JeanetteMueller/OpenPerseverance/images/progress/IMG_1283.jpeg

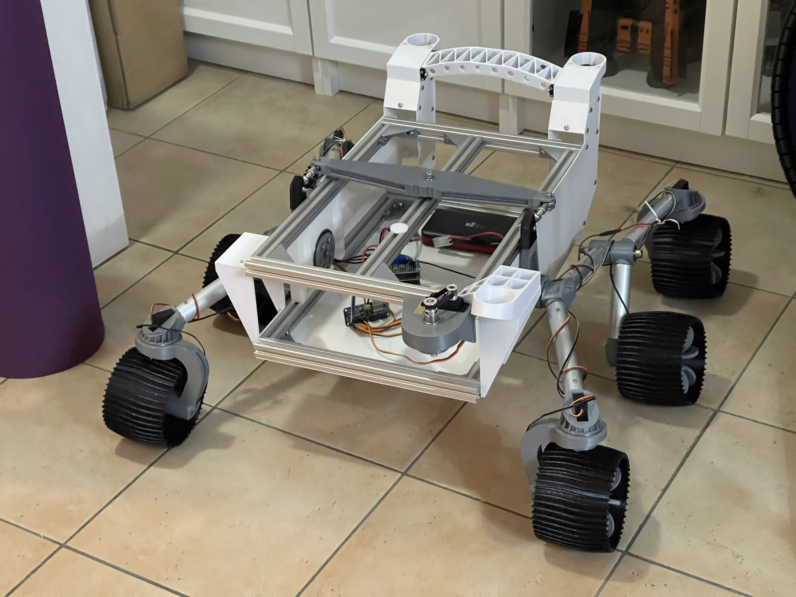
images/progress/IMG_1283.jpeg
