JeanetteMueller/OpenPerseverance/images/progress/IMG_1419.jpeg

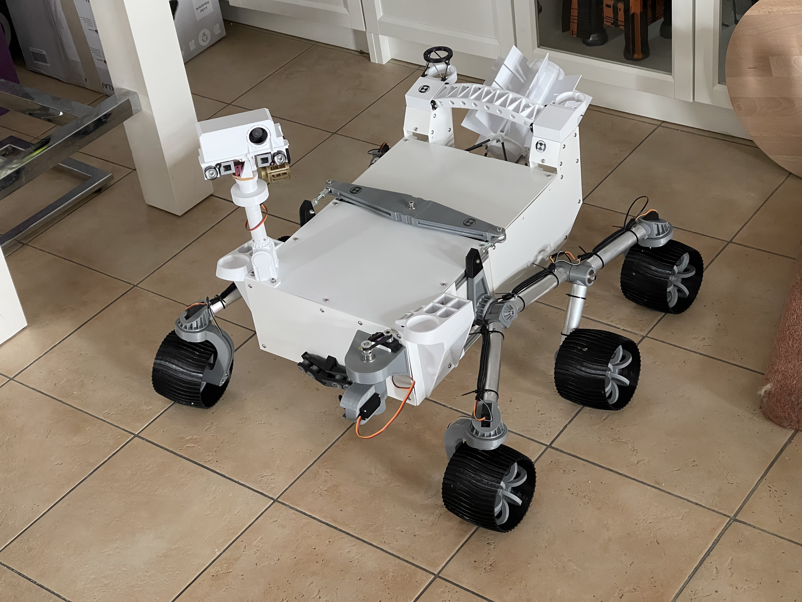
images/progress/IMG_1419.jpeg
