JeanetteMueller/OpenPerseverance/images/progress/IMG_1653.jpeg

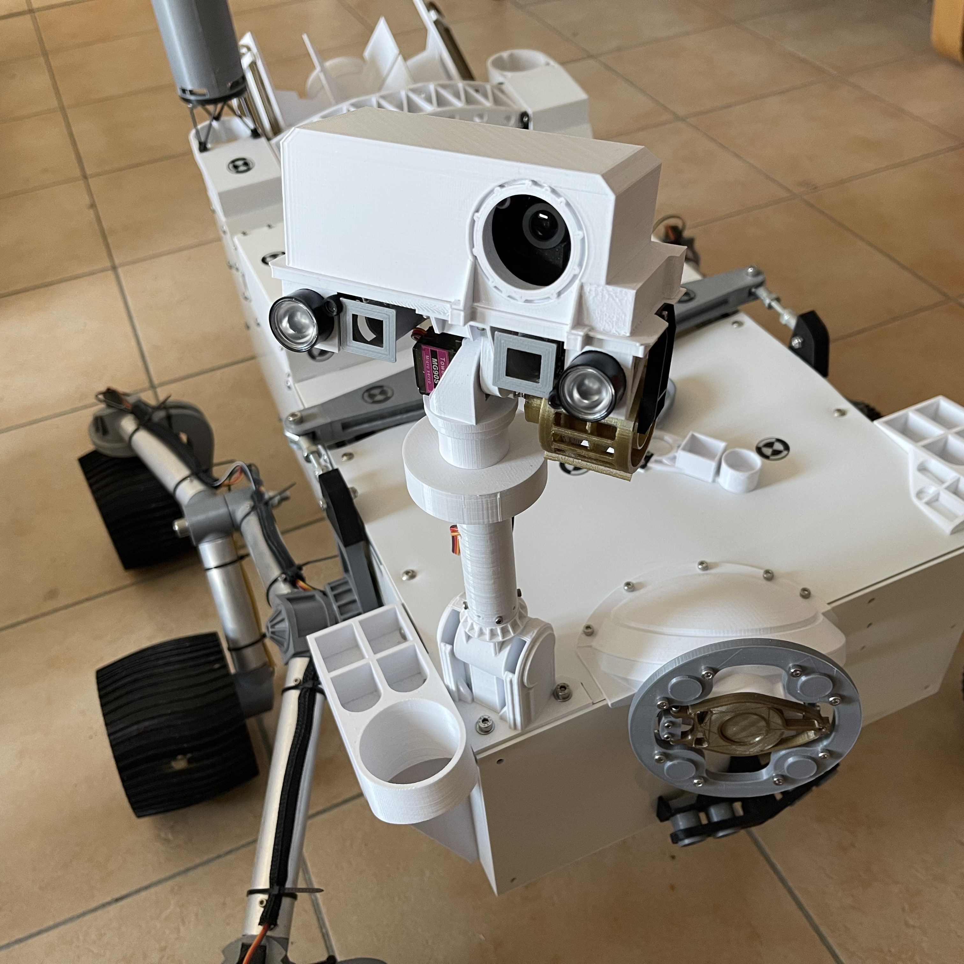
images/progress/IMG_1653.jpeg
