JeanetteMueller/OpenPerseverance/stl/MainBody/SkyCraneConnector/SkyCraneConnector CableCutter.stl

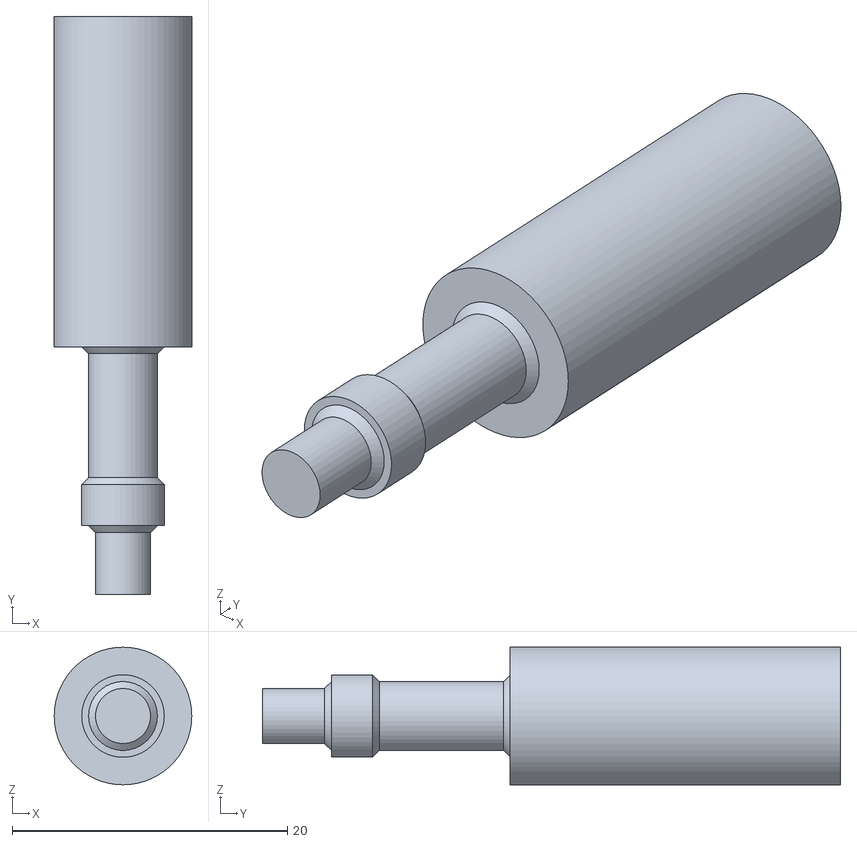
[picture p25: CAD file, 2021-09-22]
stl/MainBody/SkyCraneConnector/SkyCraneConnector CableCutter.stl
10.0 x 42.0 x 10.0
