JeanetteMueller/OpenPerseverance/stl/MainBody/Sundial/SundialBase.stl

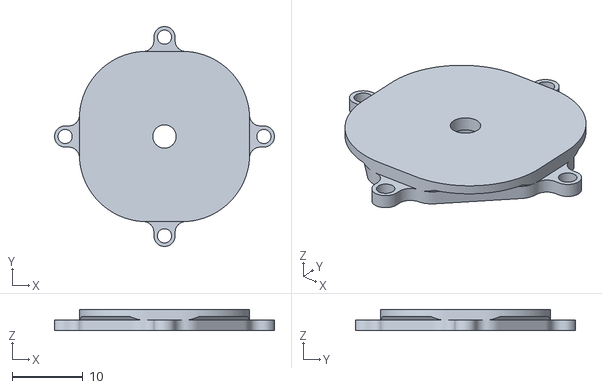
[picture p26: CAD file, 2021-06-23]
stl/MainBody/Sundial/SundialBase.stl
31.0 x 31.0 x 3.00
