JeanetteMueller/OpenPerseverance/stl/MainBody/TopBox/TopBodyBox Back.stl

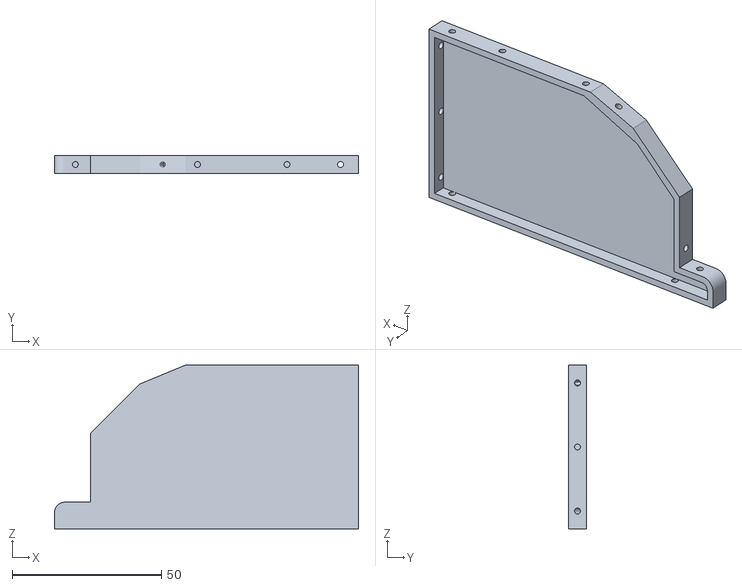
[picture p27: CAD file, 2021-09-22]
stl/MainBody/TopBox/TopBodyBox Back.stl
102.0 x 6.00 x 55.0
