JeanetteMueller/OpenPerseverance/stl/MainBody/UHF/UHF-FootRight.stl

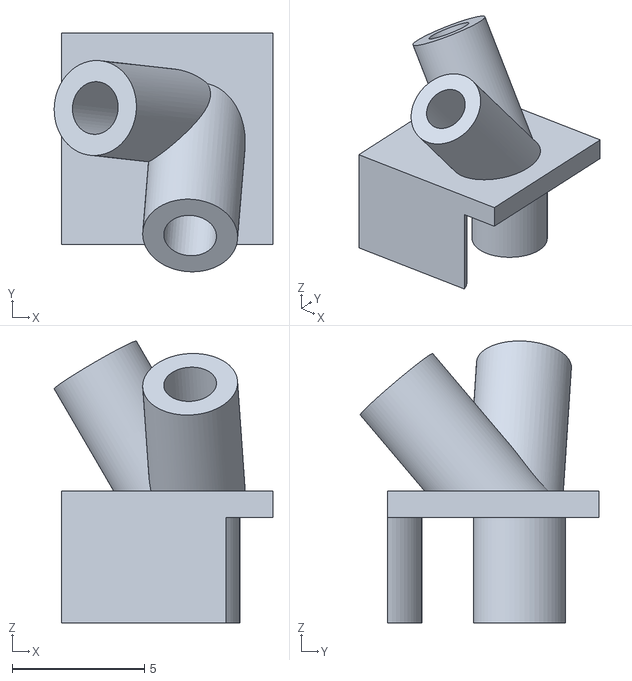
[picture p28: CAD file, 2021-04-29]
stl/MainBody/UHF/UHF-FootRight.stl
8.27 x 9.03 x 10.7
