JeanetteMueller/OpenPerseverance/stl/RockerBogie/CenterRodMount_v2.stl

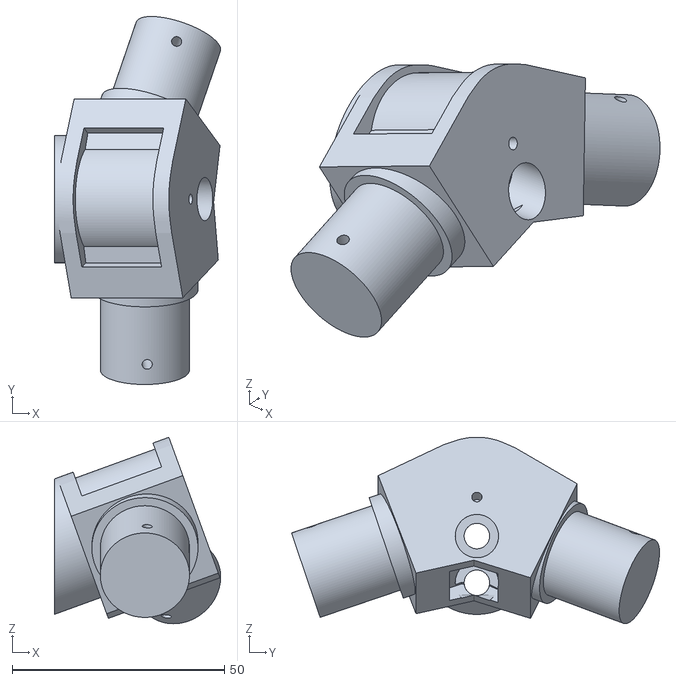
[picture p29: CAD file, 2024-09-03]
stl/RockerBogie/CenterRodMount_v2.stl
39.2 x 86.7 x 43.9
