JeanetteMueller/OpenPerseverance/stl/RockerBogie/UpdatedVersionFor37mmMotor/WheelHolder_Lower.stl

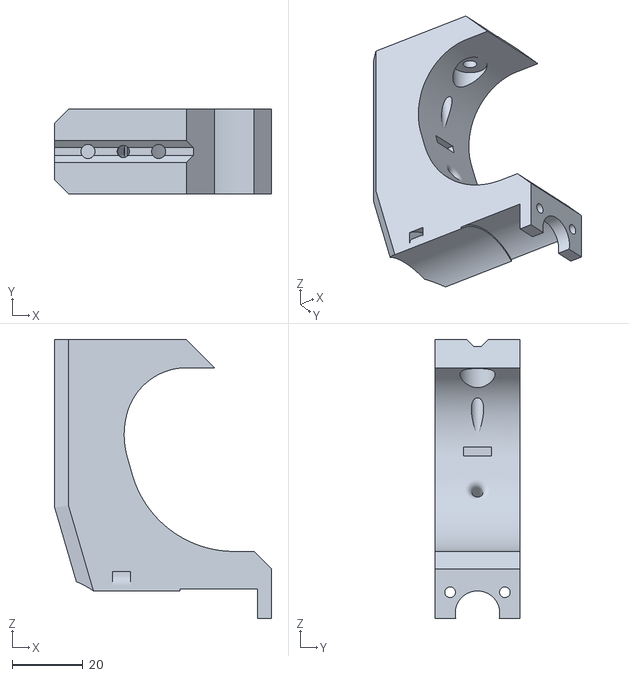
[picture p30: CAD file, 2024-09-03]
stl/RockerBogie/UpdatedVersionFor37mmMotor/WheelHolder_Lower.stl
61.5 x 24.0 x 79.0
