JeanetteMueller/OpenPerseverance/stl/Arm/Hand/HandConnector.stl

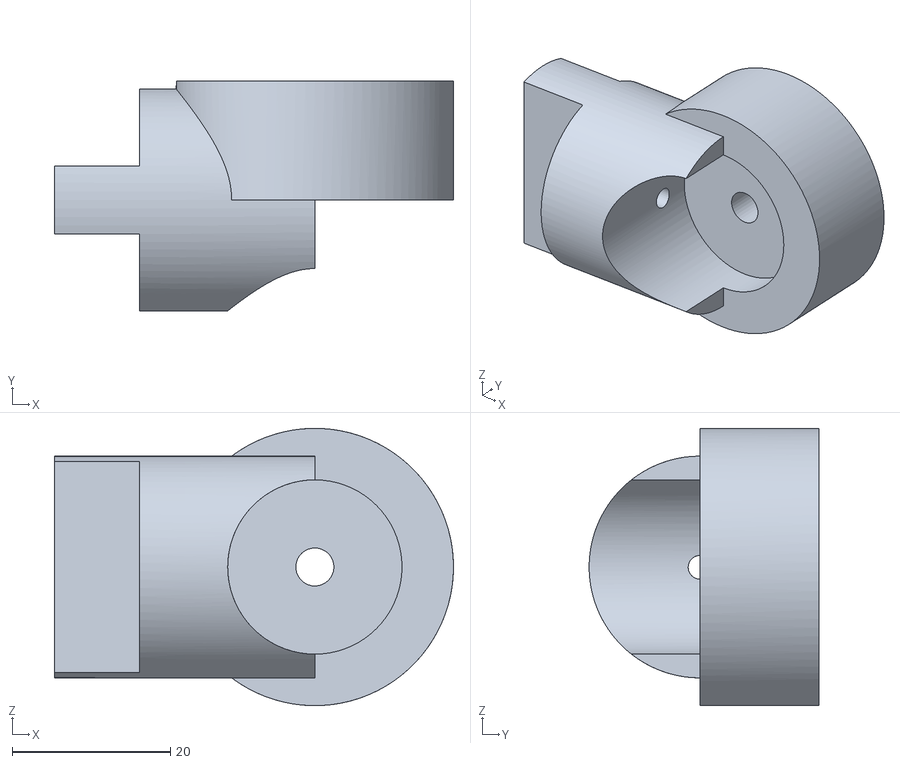
[picture p31: CAD file, 2021-10-04]
stl/Arm/Hand/HandConnector.stl
50.4 x 29.0 x 35.0
