JeanetteMueller/OpenPerseverance/stl/Arm/Instruments/InstrumentsCameraSensor.stl

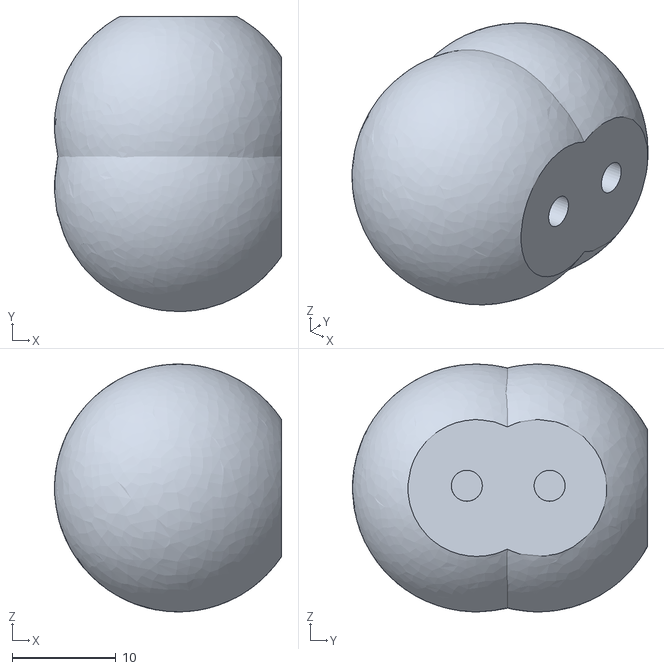
[picture p32: CAD file, 2021-10-04]
stl/Arm/Instruments/InstrumentsCameraSensor.stl
22.0 x 28.5 x 23.9
