JeanetteMueller/OpenPerseverance/stl/Arm/LowerArm/LowerArmAktuator2.stl

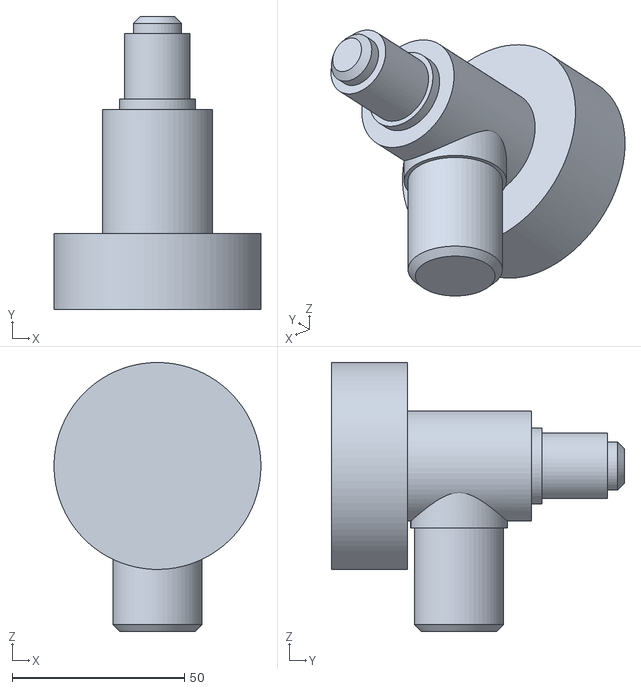
[picture p33: CAD file, 2021-10-04]
stl/Arm/LowerArm/LowerArmAktuator2.stl
60.0 x 85.0 x 78.0
