JeanetteMueller/OpenPerseverance/stl/Arm/NamePlate.stl

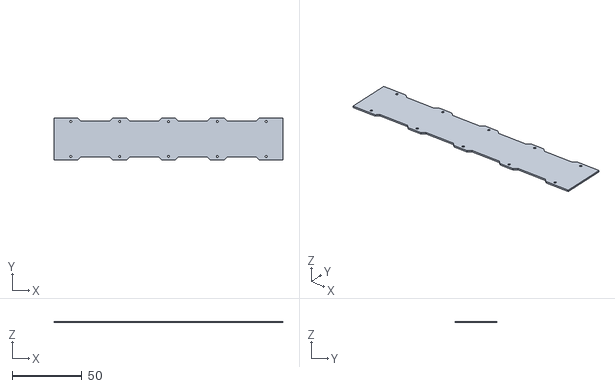
[picture p34: CAD file, 2021-10-04]
stl/Arm/NamePlate.stl
164.0 x 30.0 x 1.00
