JeanetteMueller/OpenPerseverance/stl/Arm/UpperArm/UpperArmRodConnector2.stl

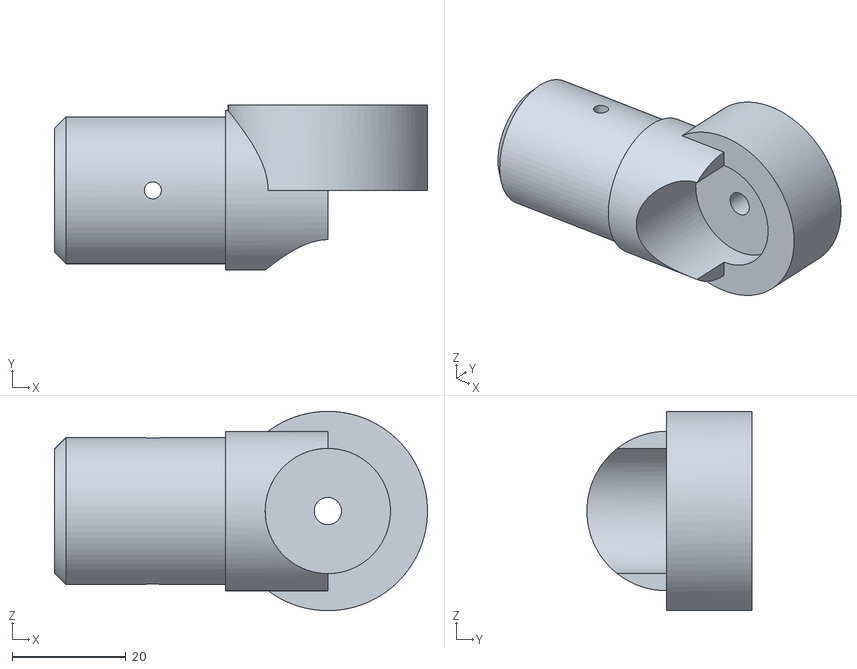
[picture p35: CAD file, 2021-10-04]
stl/Arm/UpperArm/UpperArmRodConnector2.stl
65.5 x 29.0 x 35.0
