JeanetteMueller/OpenPerseverance/stl/HeatExchanger_Left/Heatpipes/HeatExchanger Holder 2.stl

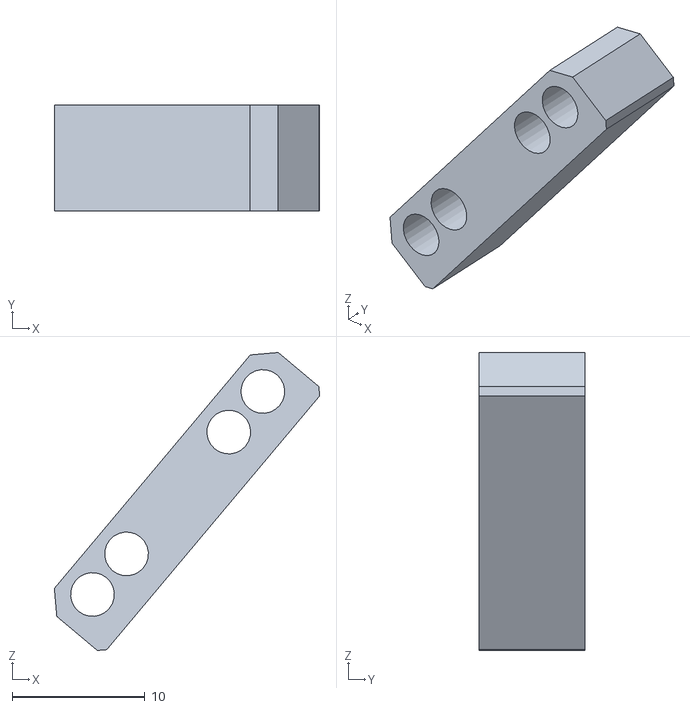
[picture p36: CAD file, 2021-09-22]
stl/HeatExchanger_Left/Heatpipes/HeatExchanger Holder 2.stl
20.0 x 8.00 x 22.5
