JeanetteMueller/OpenPerseverance/stl/HeatExchanger_Left/Holder/HeatExchangerHolder WallMountPoint.stl

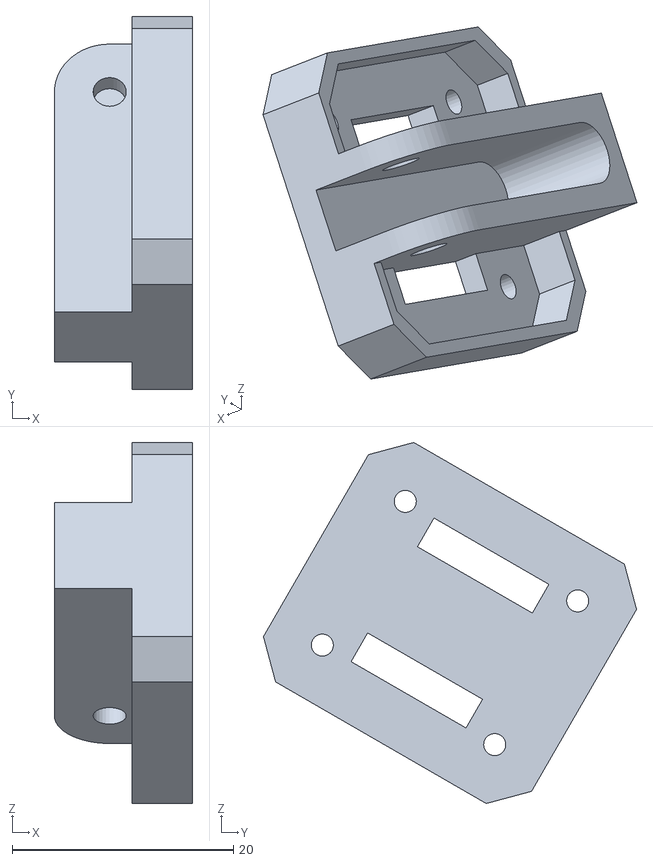
[picture p37: CAD file, 2021-09-22]
stl/HeatExchanger_Left/Holder/HeatExchangerHolder WallMountPoint.stl
12.5 x 33.7 x 32.7
