JeanetteMueller/OpenPerseverance/stl/HeatExchanger_Left/Wall/HeatExchanger Wall_Left_1.stl

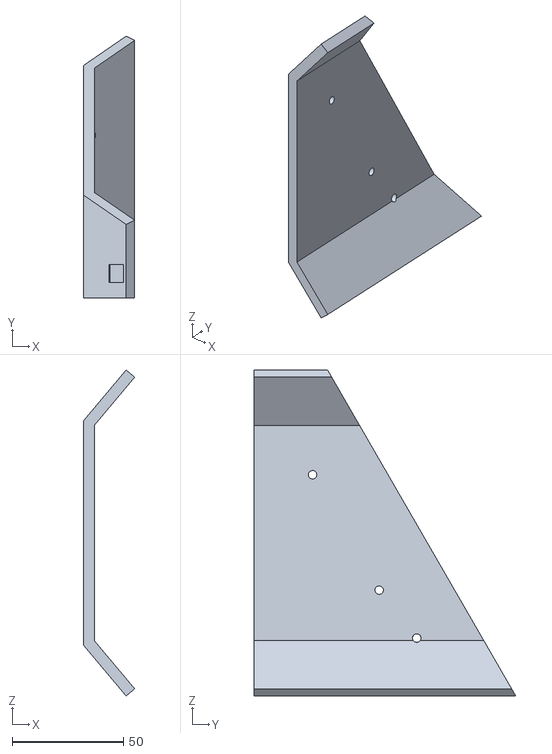
[picture p38: CAD file, 2021-09-22]
stl/HeatExchanger_Left/Wall/HeatExchanger Wall_Left_1.stl
23.2 x 117.8 x 146.8
