JeanetteMueller/OpenPerseverance/stl/MainBody/DifferentialBlocker/DifferentialBlocker Base.stl

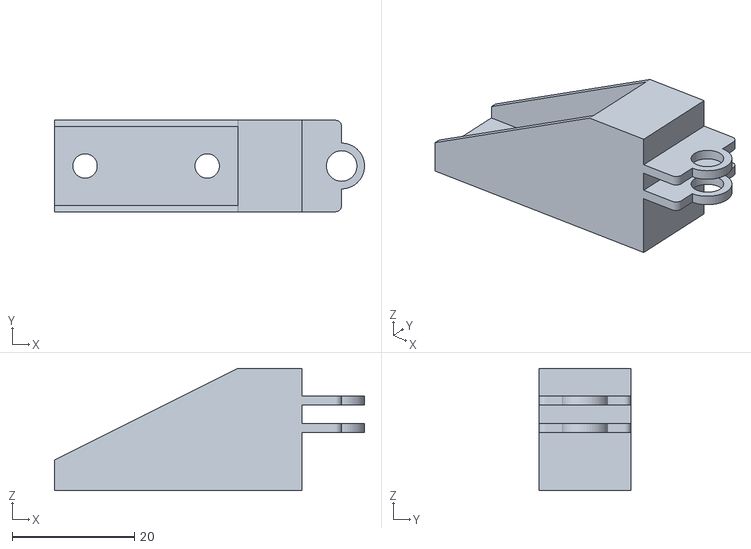
[picture p39: CAD file, 2021-09-22]
stl/MainBody/DifferentialBlocker/DifferentialBlocker Base.stl
50.7 x 15.0 x 20.0
