JeanetteMueller/OpenPerseverance/stl/MainBody/FrontBodyCamera/FrontBodyCamera.stl

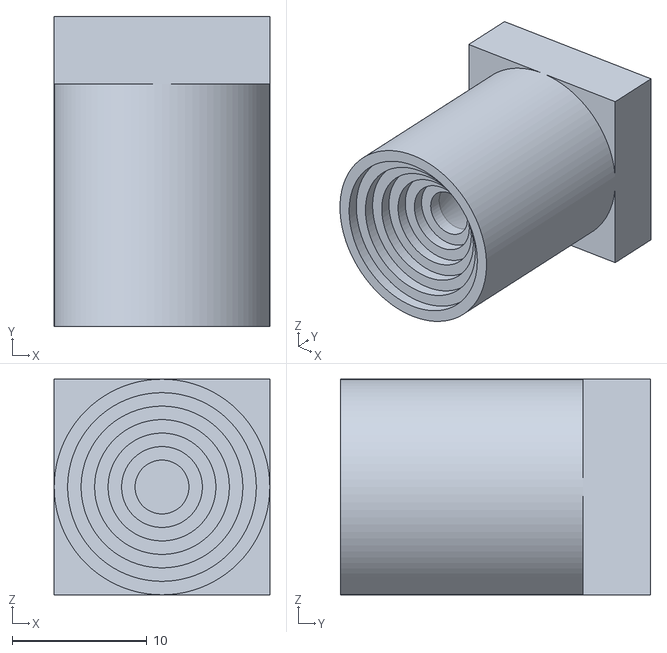
[picture p40: CAD file, 2021-05-07]
stl/MainBody/FrontBodyCamera/FrontBodyCamera.stl
16.0 x 23.0 x 16.0
