JeanetteMueller/OpenPerseverance/stl/MainBody/HighGainAntenna/HighGainAntenna RotationMotor.stl

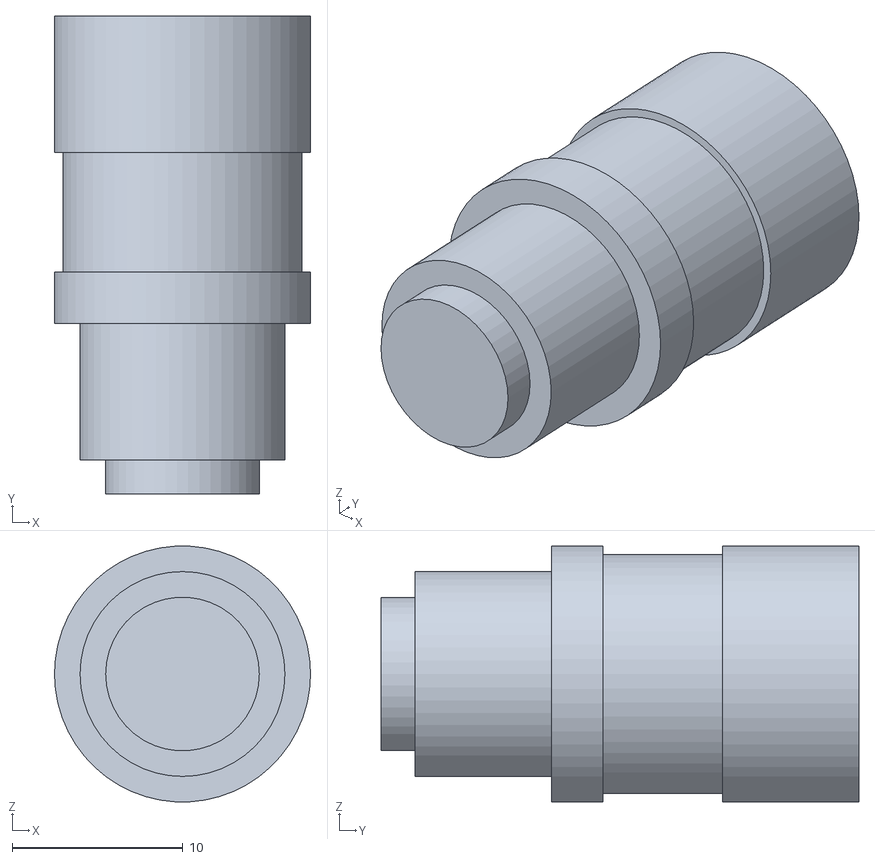
[picture p41: CAD file, 2021-09-22]
stl/MainBody/HighGainAntenna/HighGainAntenna RotationMotor.stl
15.0 x 28.0 x 15.0
