JeanetteMueller/OpenPerseverance/stl/MainBody/LowGainAntenna/LowGainAntenna Mount.stl

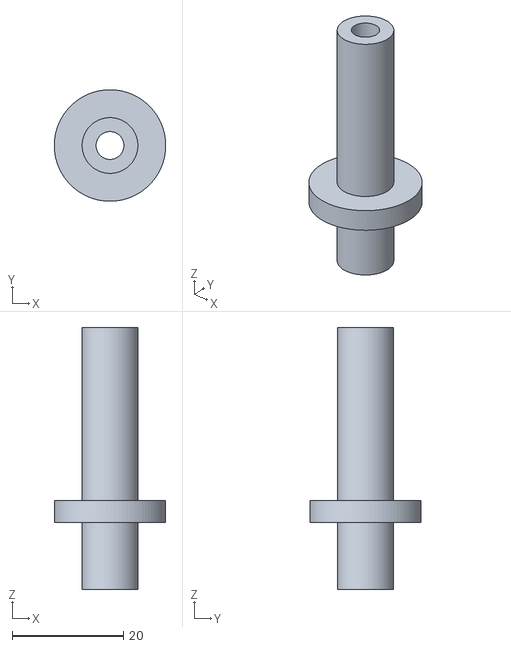
[picture p42: CAD file, 2021-09-22]
stl/MainBody/LowGainAntenna/LowGainAntenna Mount.stl
20.0 x 20.0 x 47.0
