JeanetteMueller/OpenPerseverance/stl/MainBody/SampleCollector/HatchHolderOuter.stl

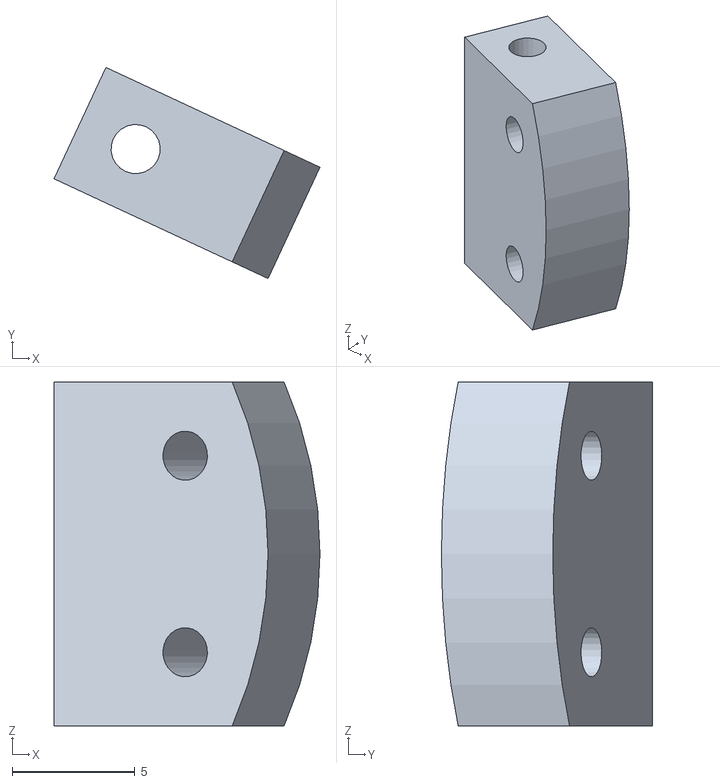
[picture p43: CAD file, 2021-06-20]
stl/MainBody/SampleCollector/HatchHolderOuter.stl
10.8 x 8.59 x 14.0
