JeanetteMueller/OpenPerseverance/stl/MainBody/ShellToProfileConnector.stl

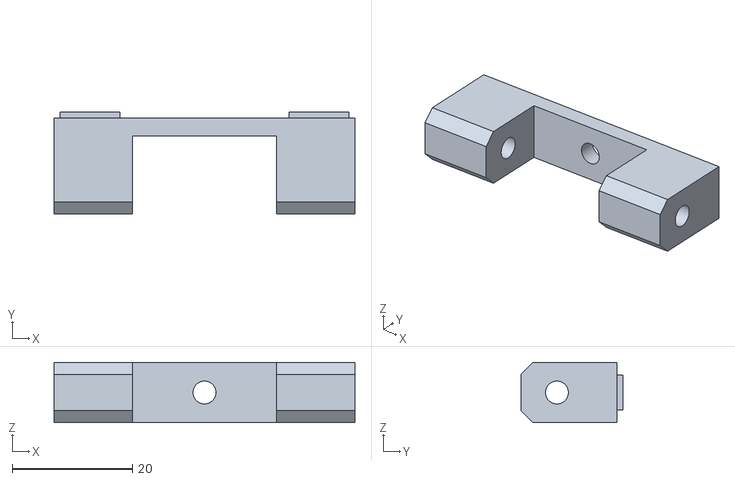
[picture p44: CAD file, 2021-04-29]
stl/MainBody/ShellToProfileConnector.stl
50.0 x 17.0 x 10.0
