JeanetteMueller/OpenPerseverance/stl/MainBody/SkyCraneConnector/SkyCraneConnector Base.stl

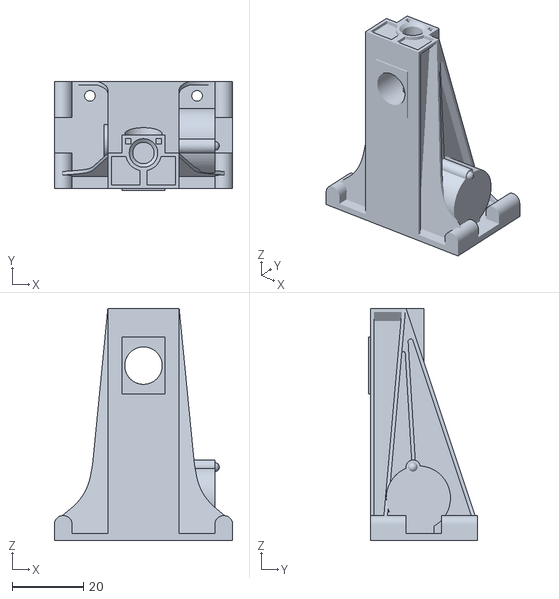
[picture p45: CAD file, 2021-09-22]
stl/MainBody/SkyCraneConnector/SkyCraneConnector Base.stl
50.0 x 30.5 x 65.0
