JeanetteMueller/OpenPerseverance/stl/MainBody/Sundial/SundialPin.stl

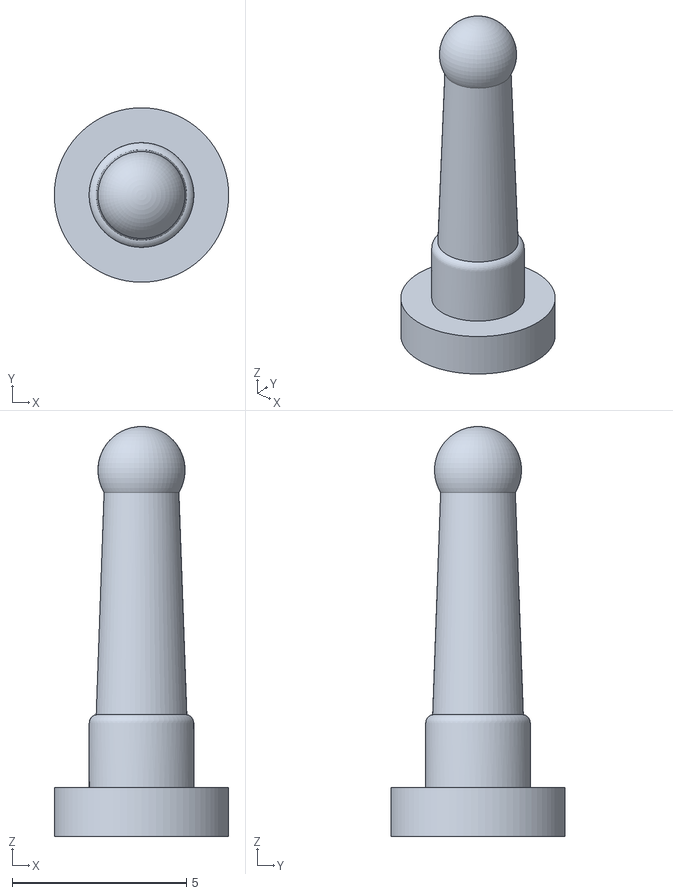
[picture p46: CAD file, 2021-06-23]
stl/MainBody/Sundial/SundialPin.stl
5.00 x 5.00 x 11.8
