JeanetteMueller/OpenPerseverance/stl/RockerBogie/DifferentialMount_v2.stl

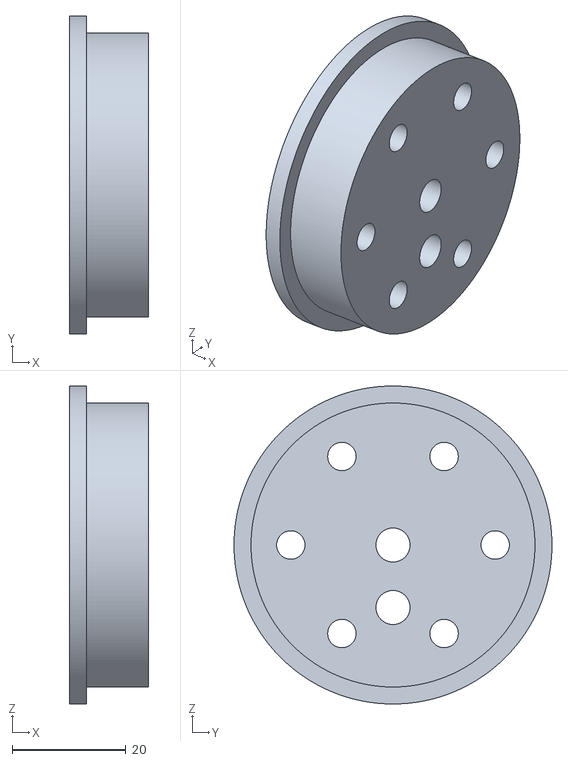
[picture p47: CAD file, 2024-09-03]
stl/RockerBogie/DifferentialMount_v2.stl
14.0 x 56.0 x 56.0
