JeanetteMueller/OpenPerseverance/stl/RockerBogie/UpdatedVersionFor37mmMotor/WheelHolderCenter.stl

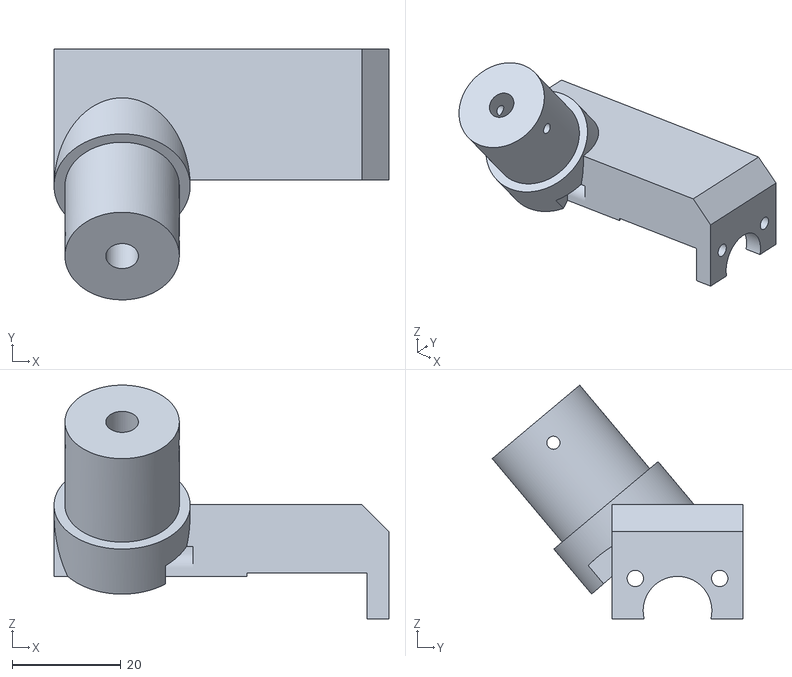
[picture p48: CAD file, 2024-09-03]
stl/RockerBogie/UpdatedVersionFor37mmMotor/WheelHolderCenter.stl
61.5 x 46.0 x 42.9
