JeanetteMueller/OpenPerseverance/stl/Arm/ArmStandReferencesMount.stl

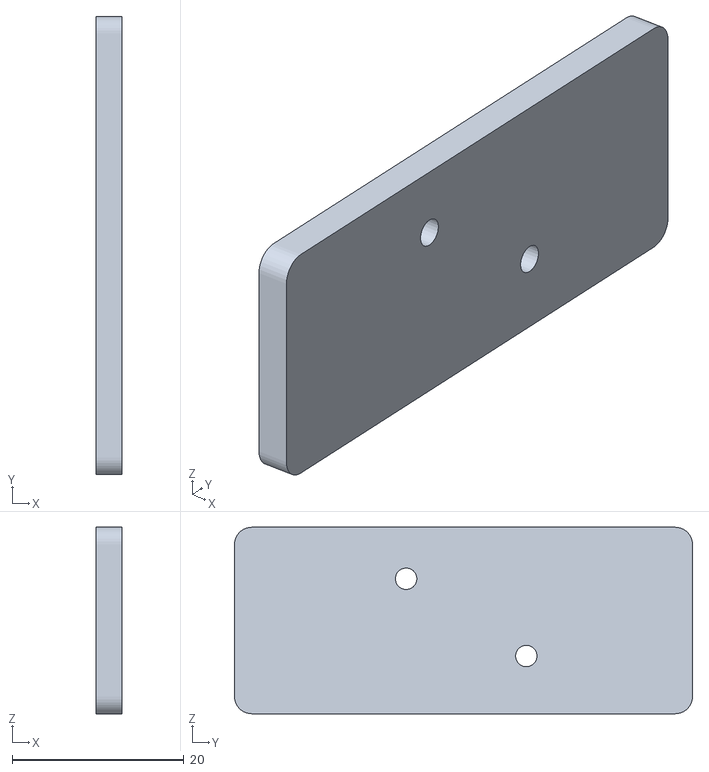
[picture p49: CAD file, 2021-10-04]
stl/Arm/ArmStandReferencesMount.stl
3.00 x 53.3 x 21.7
