JeanetteMueller/OpenPerseverance/stl/Arm/Instruments/InstrumentsSherlocWatsonBody.stl

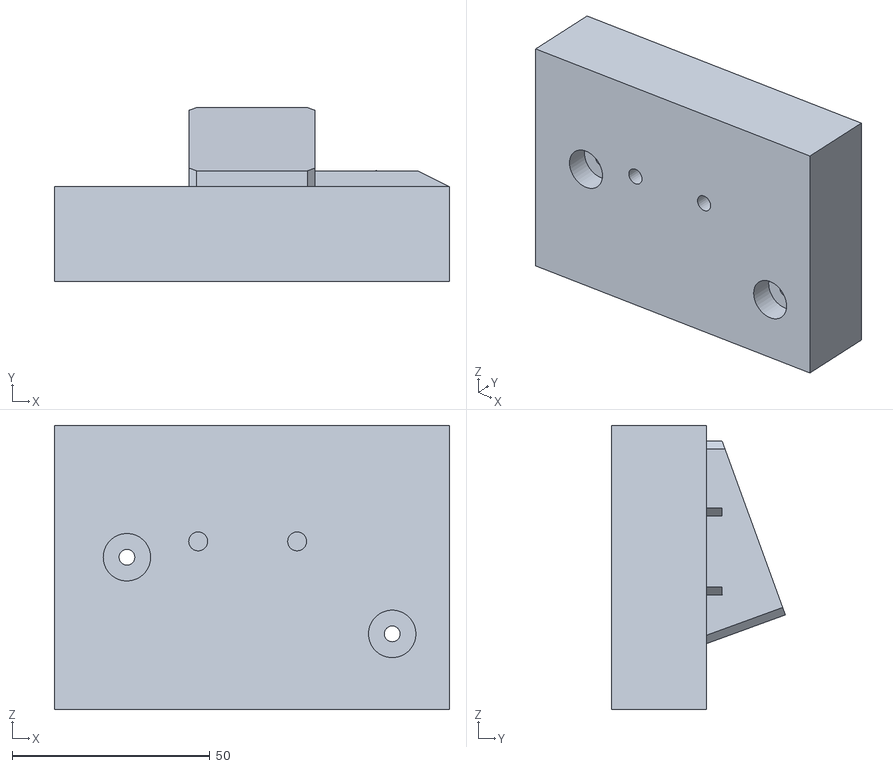
[picture p50: CAD file, 2021-10-04]
stl/Arm/Instruments/InstrumentsSherlocWatsonBody.stl
99.8 x 43.9 x 71.9
