JeanetteMueller/OpenPerseverance/stl/Arm/UpperArm/UpperArmAktuator2.stl

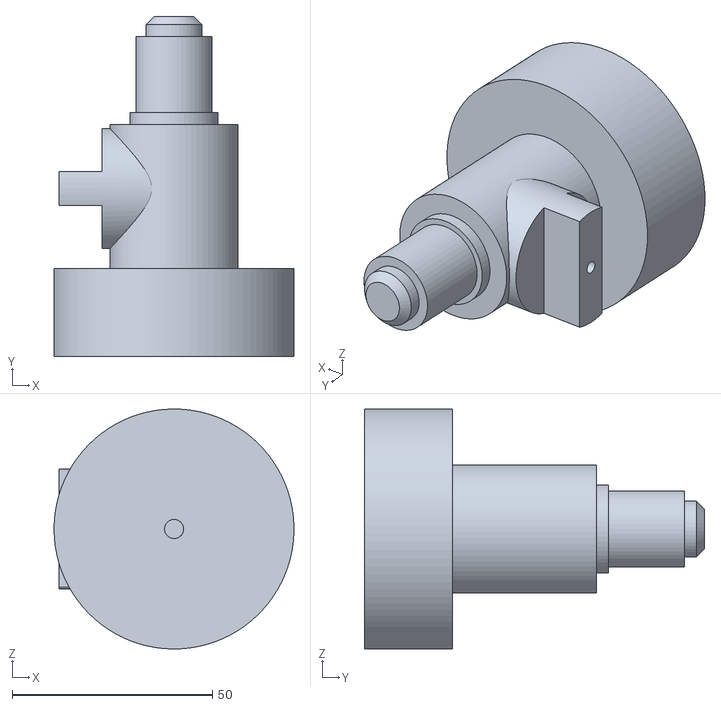
[picture p51: CAD file, 2021-10-04]
stl/Arm/UpperArm/UpperArmAktuator2.stl
60.0 x 85.0 x 60.0
