JeanetteMueller/OpenPerseverance/stl/HeatExchanger_Left/Heatpipes/HeatExchanger Holder 8.stl

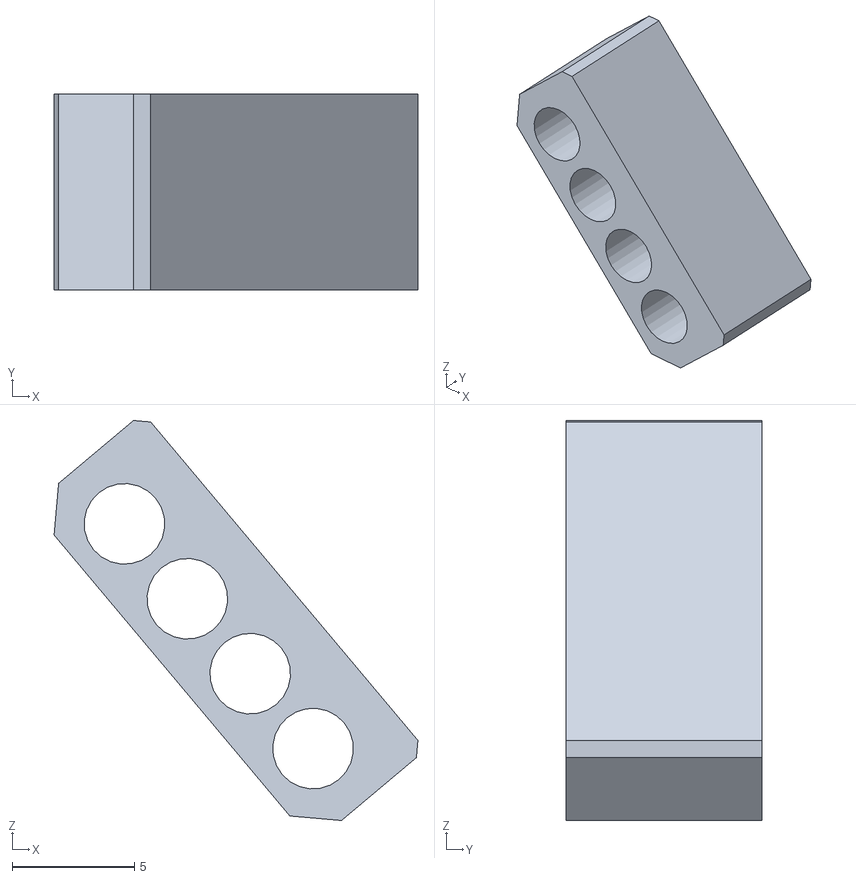
[picture p52: CAD file, 2021-09-22]
stl/HeatExchanger_Left/Heatpipes/HeatExchanger Holder 8.stl
14.9 x 8.00 x 16.4
