JeanetteMueller/OpenPerseverance/stl/HeatExchanger_Left/Holder/HeatExchangerHolder Connector.stl

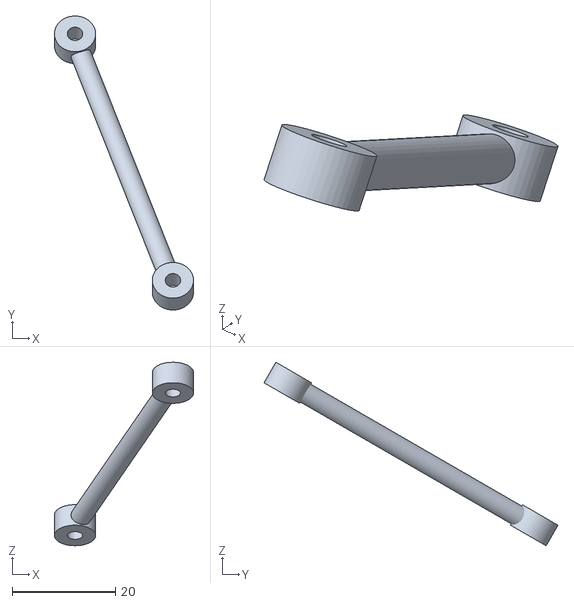
[picture p53: CAD file, 2021-09-22]
stl/HeatExchanger_Left/Holder/HeatExchangerHolder Connector.stl
27.0 x 57.1 x 35.6
