JeanetteMueller/OpenPerseverance/stl/MainBody/HighGainAntenna/HighGainAntenna RotationBase.stl

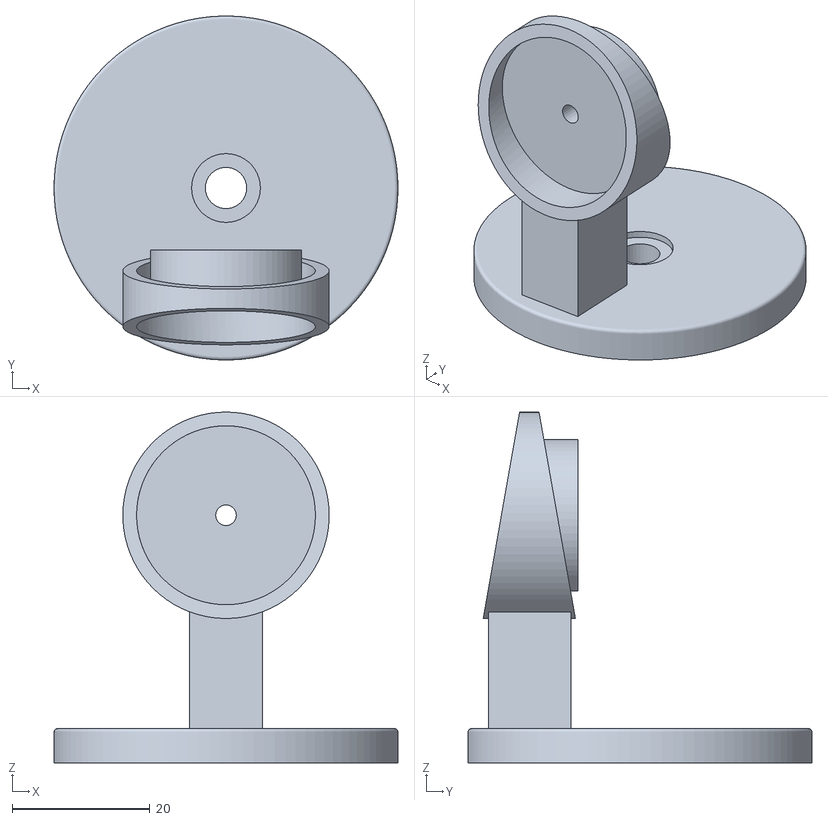
[picture p54: CAD file, 2021-09-22]
stl/MainBody/HighGainAntenna/HighGainAntenna RotationBase.stl
50.0 x 50.0 x 51.0
