JeanetteMueller/OpenPerseverance/stl/MainBody/LowGainAntenna/LowGainAntenna Foot.stl

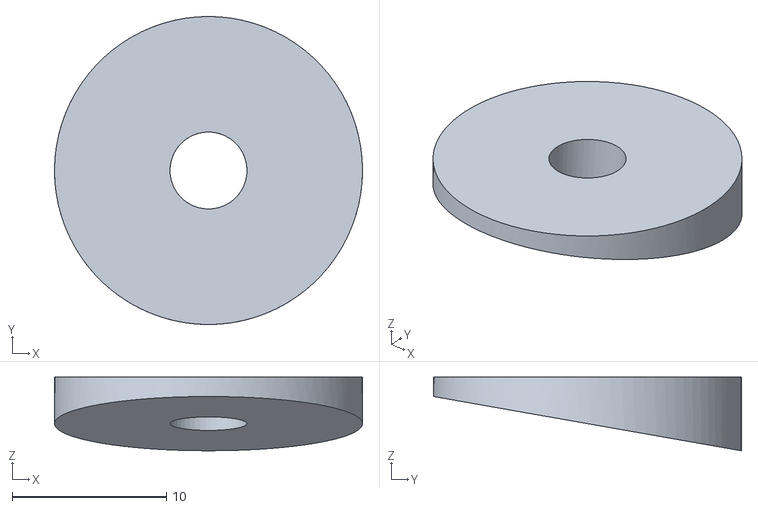
[picture p55: CAD file, 2021-09-22]
stl/MainBody/LowGainAntenna/LowGainAntenna Foot.stl
20.0 x 20.0 x 4.78
