JeanetteMueller/OpenPerseverance/stl/MainBody/SampleCollector/HatchHolderInner.stl

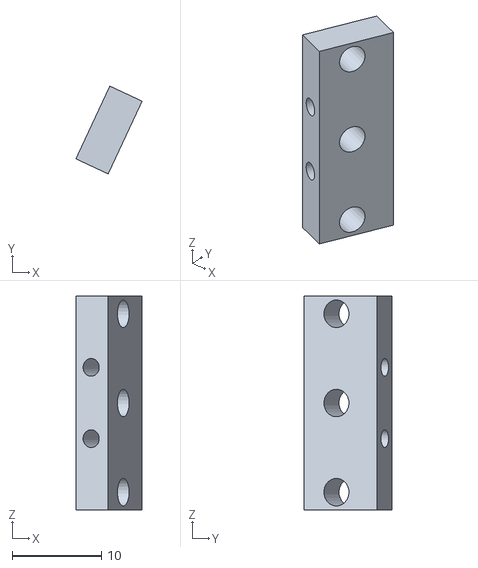
[picture p56: CAD file, 2021-06-20]
stl/MainBody/SampleCollector/HatchHolderInner.stl
7.43 x 9.85 x 24.0
