JeanetteMueller/OpenPerseverance/stl/MainBody/ShellConnector.stl

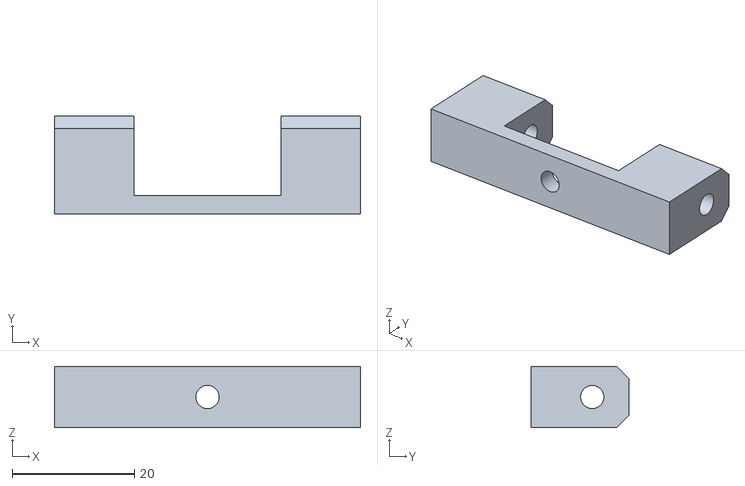
[picture p57: CAD file, 2021-04-29]
stl/MainBody/ShellConnector.stl
50.0 x 16.0 x 10.0
