JeanetteMueller/OpenPerseverance/stl/MainBody/UHF/UHF-MountingRing.stl

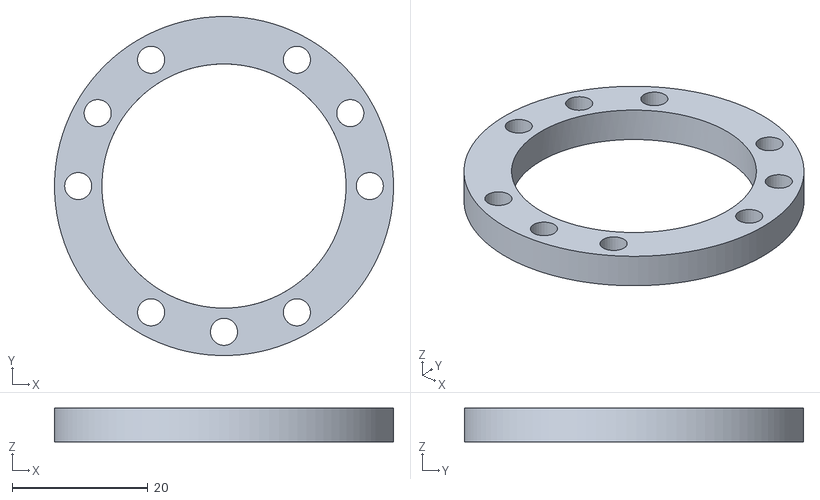
[picture p58: CAD file, 2021-04-29]
stl/MainBody/UHF/UHF-MountingRing.stl
50.0 x 50.0 x 5.00
