JeanetteMueller/OpenPerseverance/stl/RockerBogie/BalanceArmBlockerHead.stl

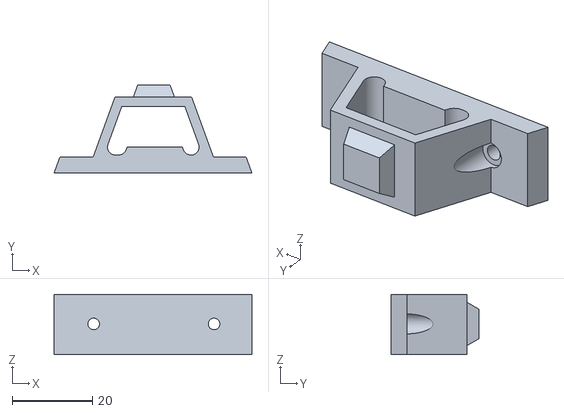
[picture p59: CAD file, 2022-03-11]
stl/RockerBogie/BalanceArmBlockerHead.stl
49.3 x 22.0 x 15.0
