JeanetteMueller/OpenPerseverance/stl/RockerBogie/UpdatedVersionFor37mmMotor/WheelHolder_Top.stl

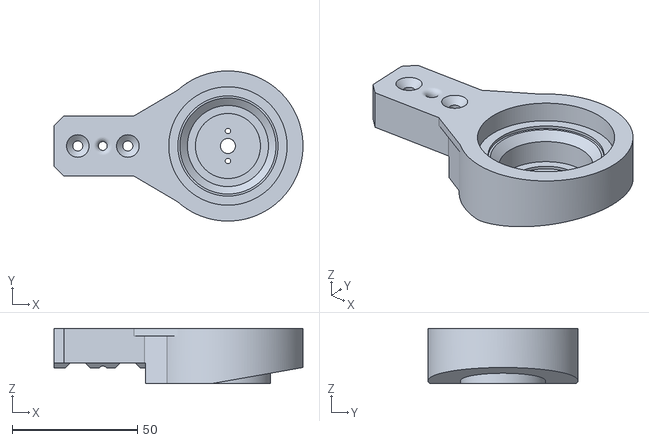
[picture p60: CAD file, 2024-09-03]
stl/RockerBogie/UpdatedVersionFor37mmMotor/WheelHolder_Top.stl
99.5 x 60.0 x 22.0
