JeanetteMueller/OpenPerseverance/stl/Arm/ArmHolder.stl

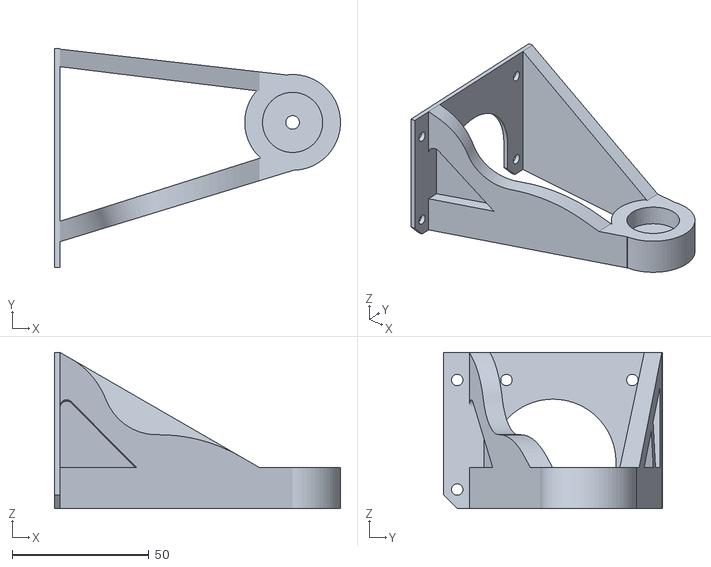
[picture p61: CAD file, 2021-10-04]
stl/Arm/ArmHolder.stl
104.5 x 80.0 x 57.1
