JeanetteMueller/OpenPerseverance/stl/Arm/Instruments/InstrumentsBaseplateConnector.stl

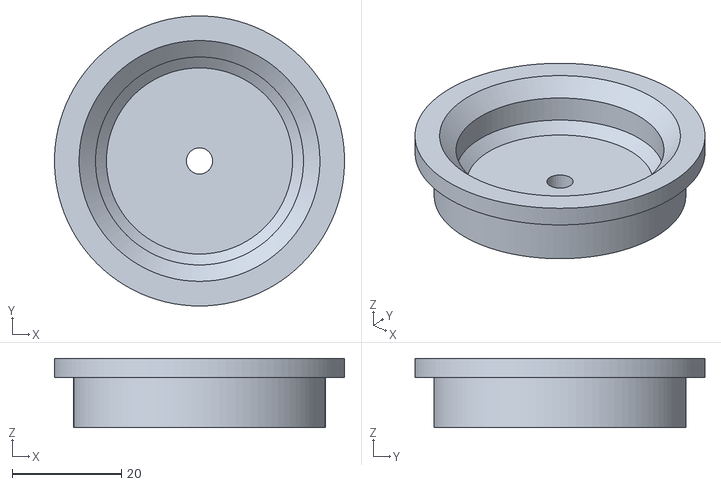
[picture p62: CAD file, 2021-10-04]
stl/Arm/Instruments/InstrumentsBaseplateConnector.stl
53.0 x 53.0 x 12.7
