JeanetteMueller/OpenPerseverance/stl/HeatExchanger_Left/Heatpipes/HeatExchanger Holder 3.stl

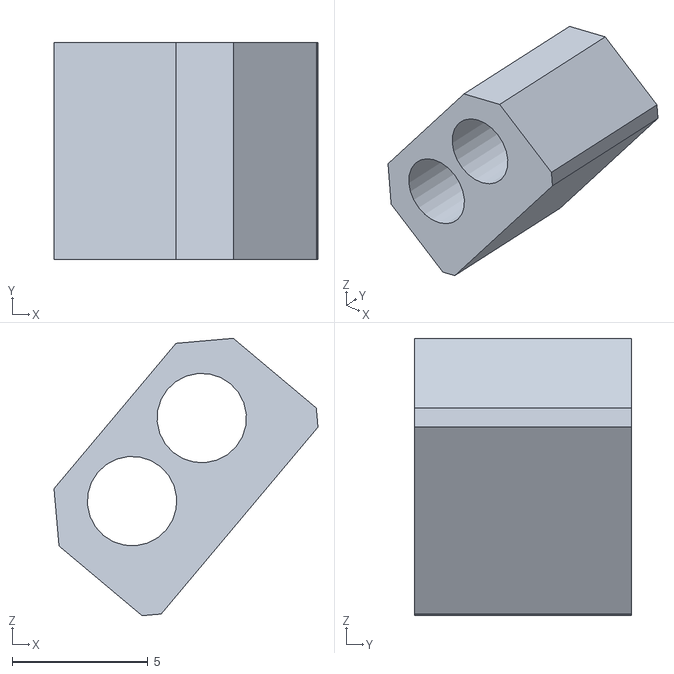
[picture p63: CAD file, 2021-09-22]
stl/HeatExchanger_Left/Heatpipes/HeatExchanger Holder 3.stl
9.74 x 8.00 x 10.2
