JeanetteMueller/OpenPerseverance/stl/MainBody/DifferentialBodyMount_v1.stl

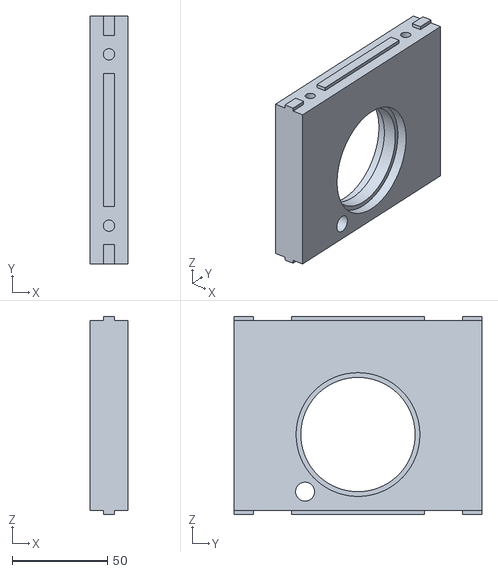
[picture p64: CAD file, 2021-04-12]
stl/MainBody/DifferentialBodyMount_v1.stl
20.0 x 130.0 x 104.0
