JeanetteMueller/OpenPerseverance/stl/MainBody/HighGainAntenna/HighGainAntenna RecieverPlate.stl

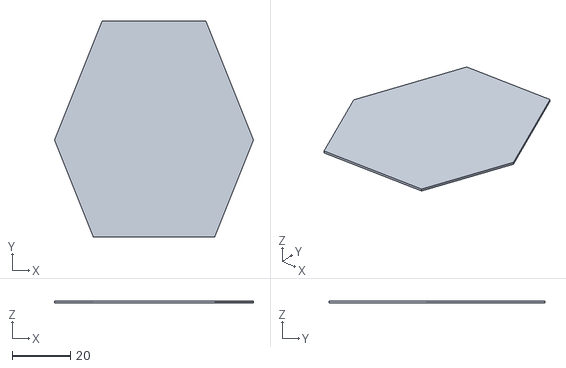
[picture p65: CAD file, 2021-09-22]
stl/MainBody/HighGainAntenna/HighGainAntenna RecieverPlate.stl
68.2 x 74.0 x 0.75
