JeanetteMueller/OpenPerseverance/stl/MainBody/SampleCollector/Hatch.stl

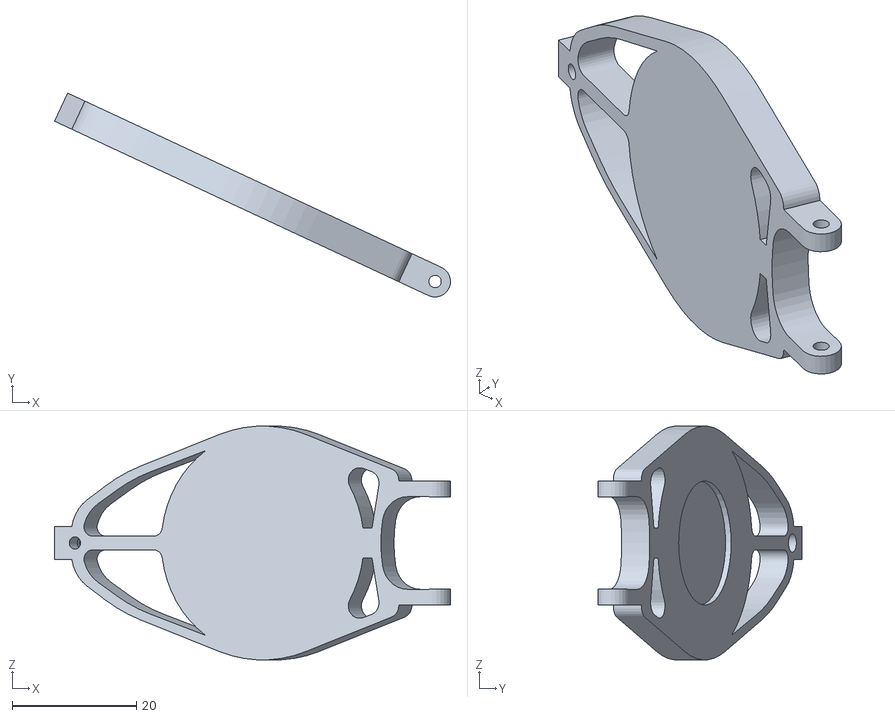
[picture p66: CAD file, 2021-06-20]
stl/MainBody/SampleCollector/Hatch.stl
63.8 x 32.9 x 37.6
