JeanetteMueller/OpenPerseverance/stl/MainBody/UHF/UHF-FootCenter.stl

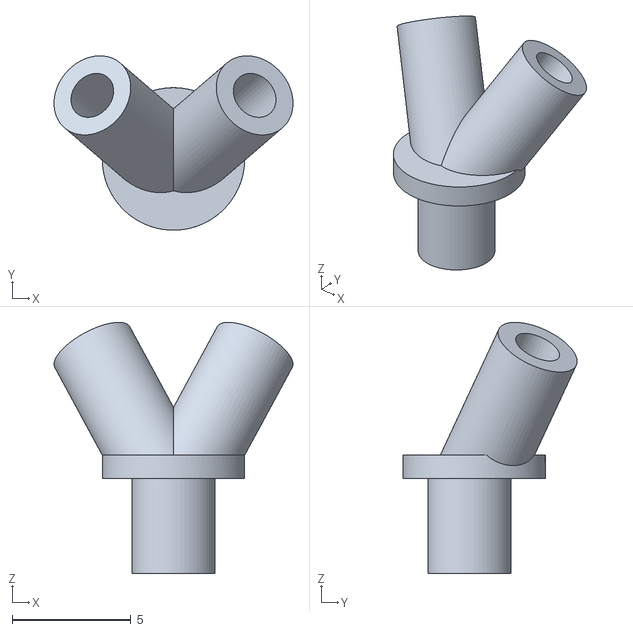
[picture p67: CAD file, 2021-04-29]
stl/MainBody/UHF/UHF-FootCenter.stl
10.1 x 7.34 x 10.6
