JeanetteMueller/OpenPerseverance/stl/RockerBogie/BalanceArmCenter.stl

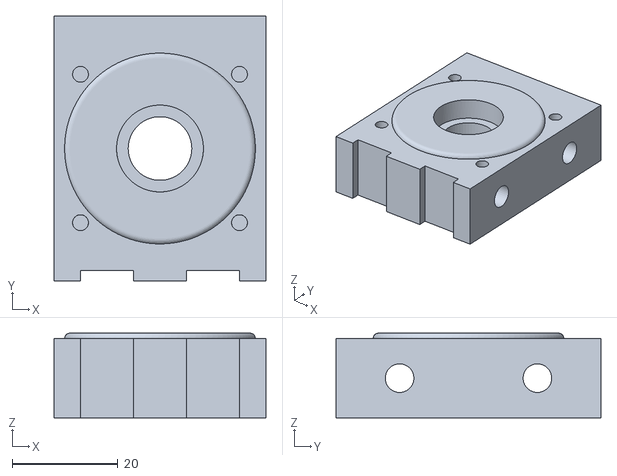
[picture p68: CAD file, 2022-03-11]
stl/RockerBogie/BalanceArmCenter.stl
40.0 x 50.0 x 16.0
