JeanetteMueller/OpenPerseverance/stl/RockerBogie/UpdatedVersionFor37mmMotor/WheelHolderServoConnector.stl

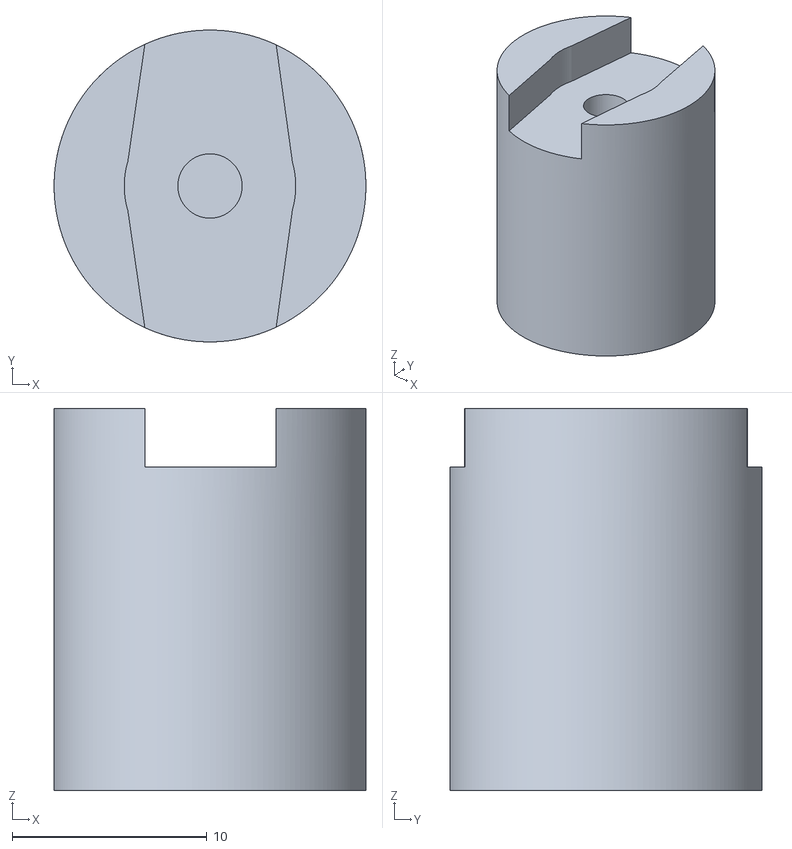
[picture p69: CAD file, 2024-09-03]
stl/RockerBogie/UpdatedVersionFor37mmMotor/WheelHolderServoConnector.stl
16.0 x 16.0 x 19.6
