JeanetteMueller/OpenPerseverance/stl/Arm/ArmStand.stl

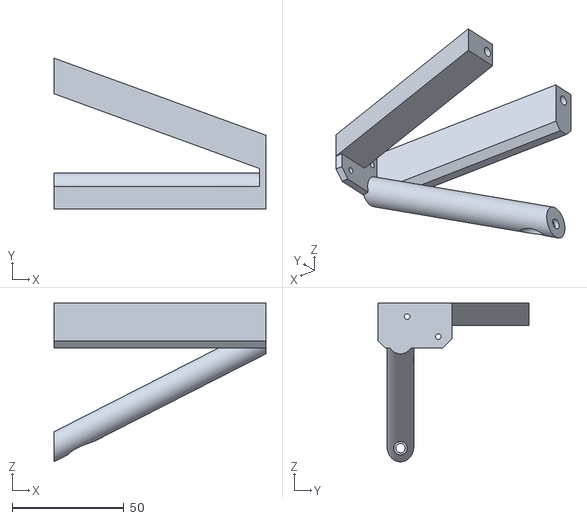
[picture p70: CAD file, 2021-10-04]
stl/Arm/ArmStand.stl
95.0 x 67.6 x 71.1
