JeanetteMueller/OpenPerseverance/stl/Arm/Instruments/InstrumentsPixl.stl

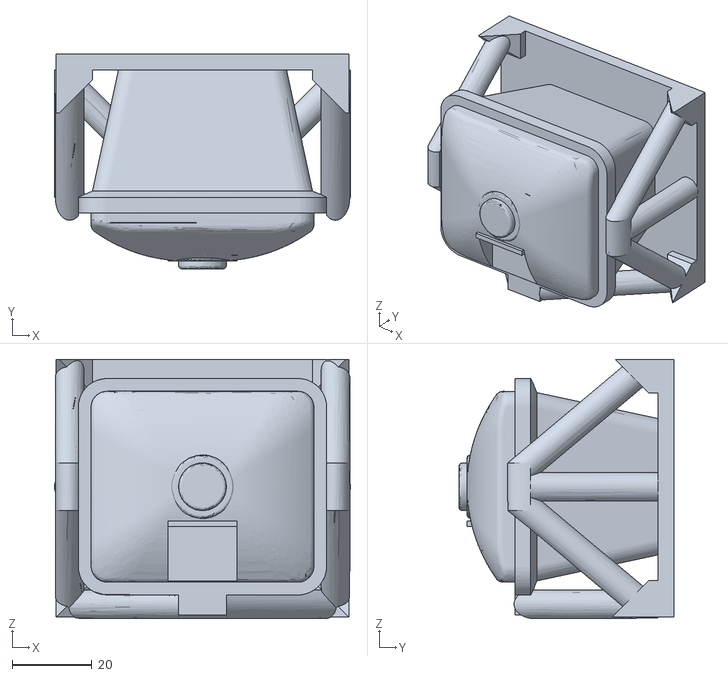
[picture p71: CAD file, 2021-10-04]
stl/Arm/Instruments/InstrumentsPixl.stl
74.3 x 53.9 x 65.0
