JeanetteMueller/OpenPerseverance/stl/MainBody/HighGainAntenna/HighGainAntenna TransportLock.stl

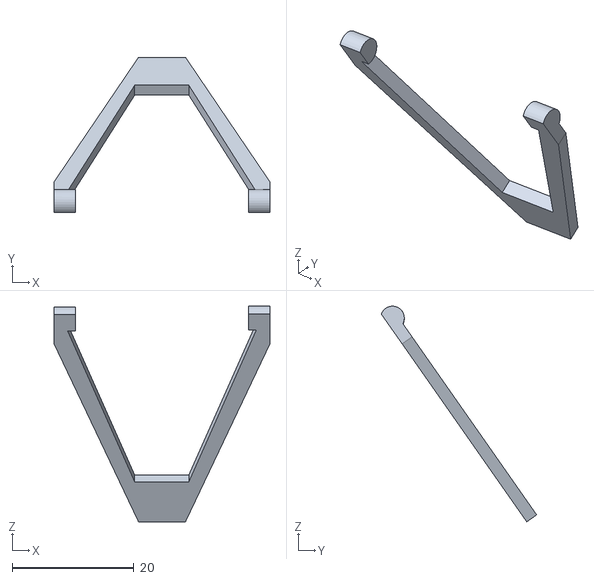
[picture p72: CAD file, 2021-09-22]
stl/MainBody/HighGainAntenna/HighGainAntenna TransportLock.stl
35.5 x 25.5 x 35.4
