JeanetteMueller/OpenPerseverance/stl/MainBody/SampleCollector/CollectorTop.stl

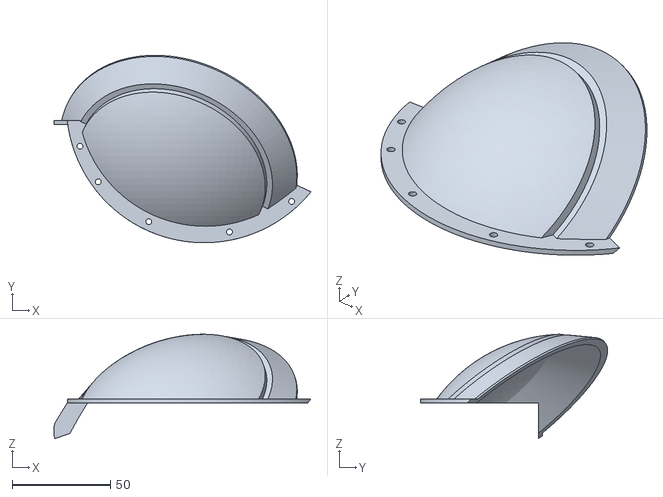
[picture p73: CAD file, 2021-06-20]
stl/MainBody/SampleCollector/CollectorTop.stl
130.6 x 95.3 x 53.1
