JeanetteMueller/OpenPerseverance/stl/RockerBogie/BalanceArm.stl

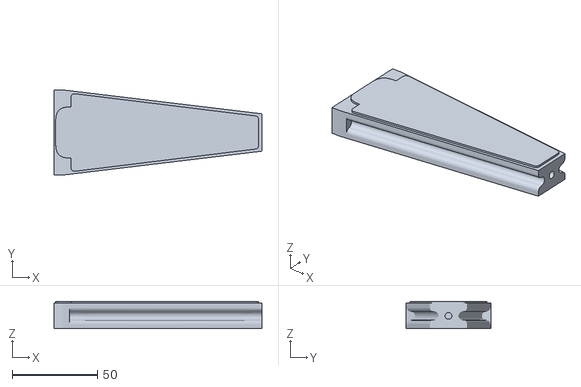
[picture p74: CAD file, 2022-03-11]
stl/RockerBogie/BalanceArm.stl
122.0 x 50.0 x 16.0
