JeanetteMueller/OpenPerseverance/stl/RockerBogie/UpdatedVersionFor37mmMotor/WheelAdapter.stl

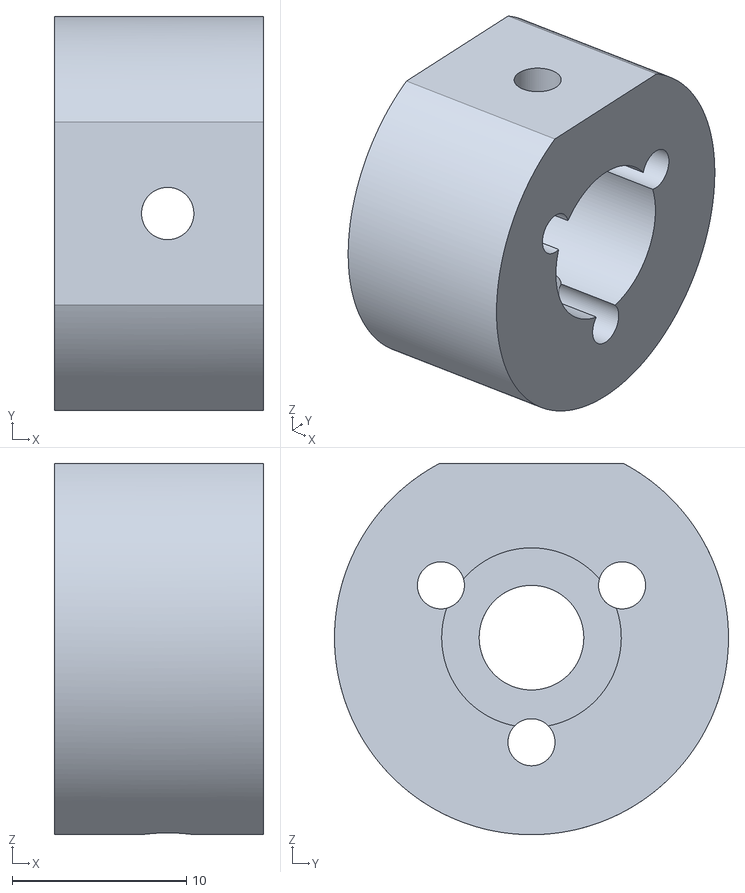
[picture p75: CAD file, 2024-09-03]
stl/RockerBogie/UpdatedVersionFor37mmMotor/WheelAdapter.stl
12.0 x 22.6 x 21.3
