JeanetteMueller/OpenPerseverance/stl/Arm/Instruments/InstrumentsBaseplate.stl

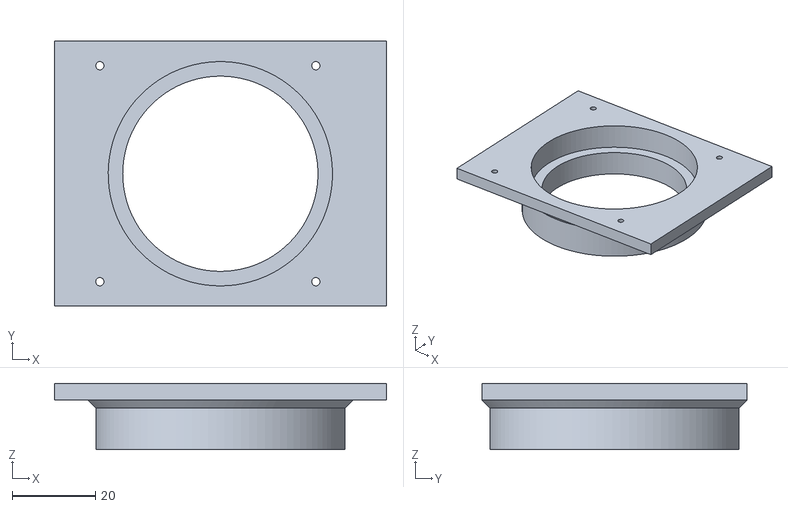
[picture p76: CAD file, 2021-10-04]
stl/Arm/Instruments/InstrumentsBaseplate.stl
79.9 x 63.9 x 16.0
