JeanetteMueller/OpenPerseverance/stl/Arm/NamePlateHolder.stl

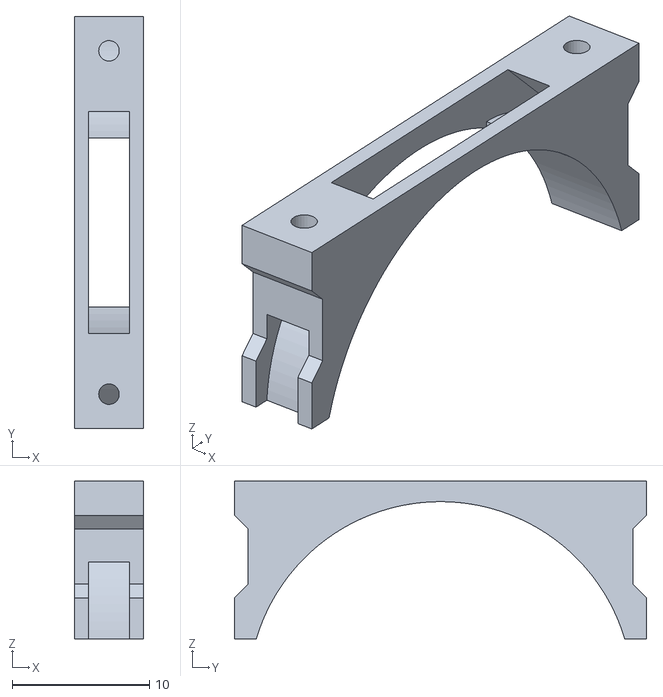
[picture p77: CAD file, 2021-10-04]
stl/Arm/NamePlateHolder.stl
5.00 x 30.0 x 11.5
