JeanetteMueller/OpenPerseverance/stl/HeatExchanger_Left/Heatpipes/HeatExchanger Holder 4.stl

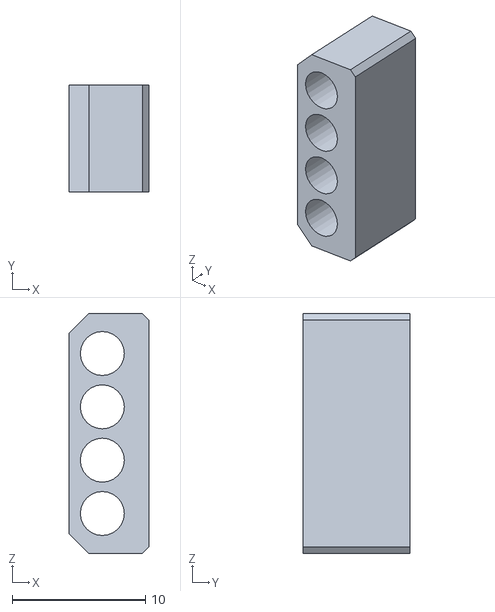
[picture p78: CAD file, 2021-09-22]
stl/HeatExchanger_Left/Heatpipes/HeatExchanger Holder 4.stl
6.00 x 8.00 x 18.0
