JeanetteMueller/OpenPerseverance/stl/MainBody/HighGainAntenna/HighGainAntenna Base.stl

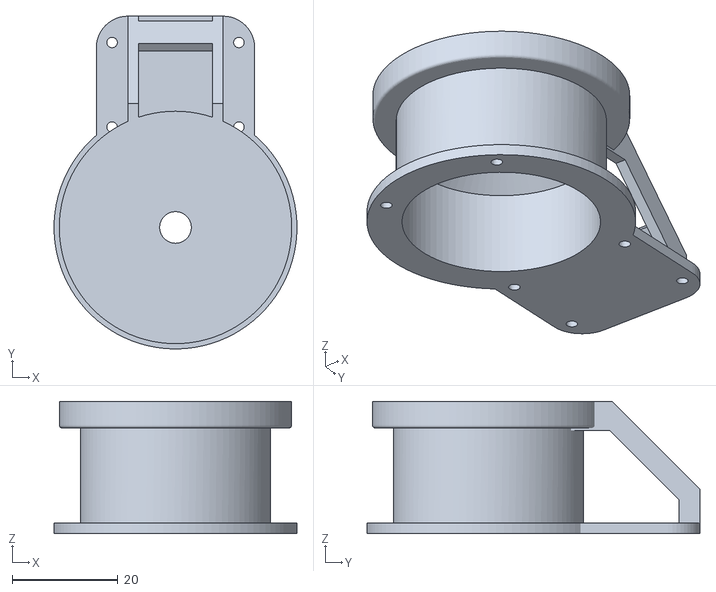
[picture p79: CAD file, 2021-09-22]
stl/MainBody/HighGainAntenna/HighGainAntenna Base.stl
46.0 x 63.0 x 25.0
