JeanetteMueller/OpenPerseverance/stl/RockerBogie/BoogieCenterExternal.stl

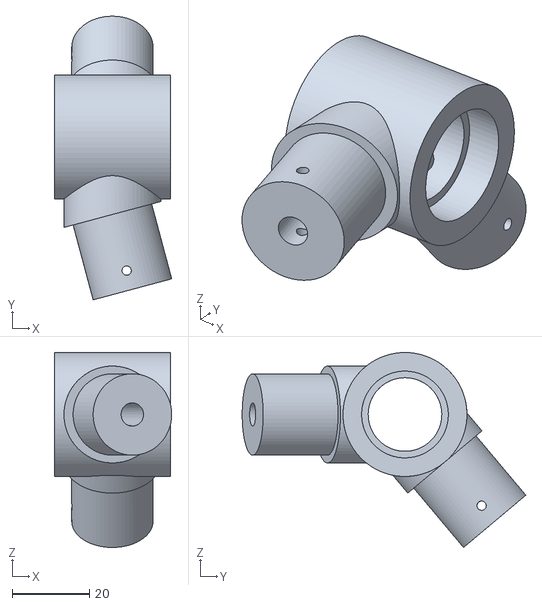
[picture p80: CAD file, 2021-10-13]
stl/RockerBogie/BoogieCenterExternal.stl
30.3 x 73.2 x 50.3
