JeanetteMueller/OpenPerseverance/stl/Arm/Instruments/InstrumentsSherlocWatsonSensor2.stl

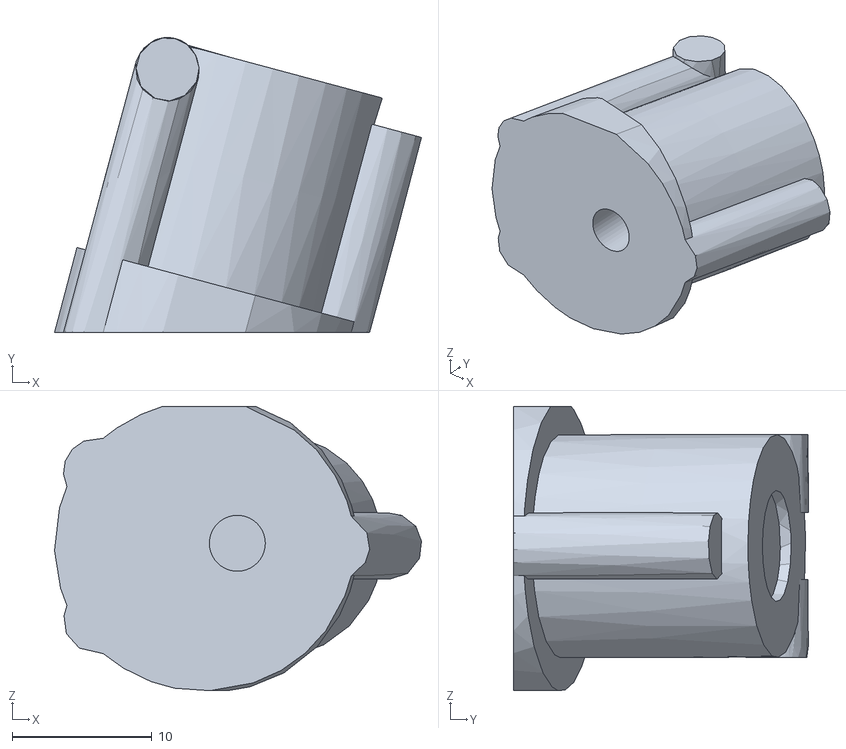
[picture p81: CAD file, 2021-10-04]
stl/Arm/Instruments/InstrumentsSherlocWatsonSensor2.stl
26.2 x 21.1 x 20.3
