JeanetteMueller/OpenPerseverance/stl/MainBody/HighGainAntenna/HighGainAntenna Holder.step

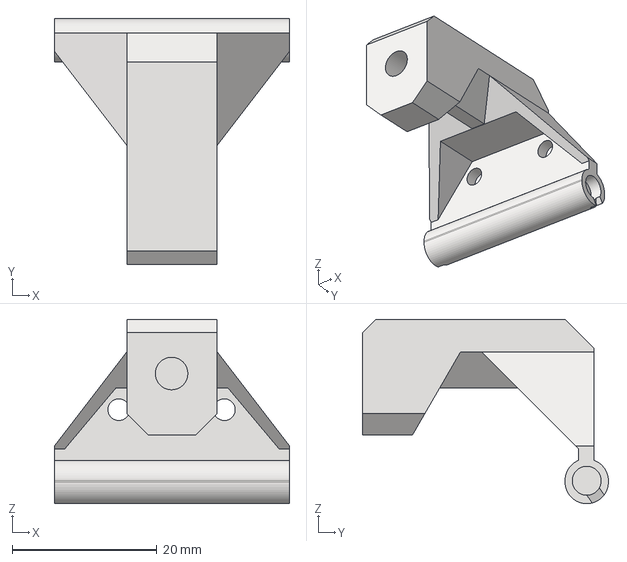
[picture p82: CAD file, 2021-09-22]
stl/MainBody/HighGainAntenna/HighGainAntenna Holder.step
32.5 x 34.0 x 25.5 mm
