JeanetteMueller/OpenPerseverance/stl/Arm/Instruments/InstrumentsCamera.stl

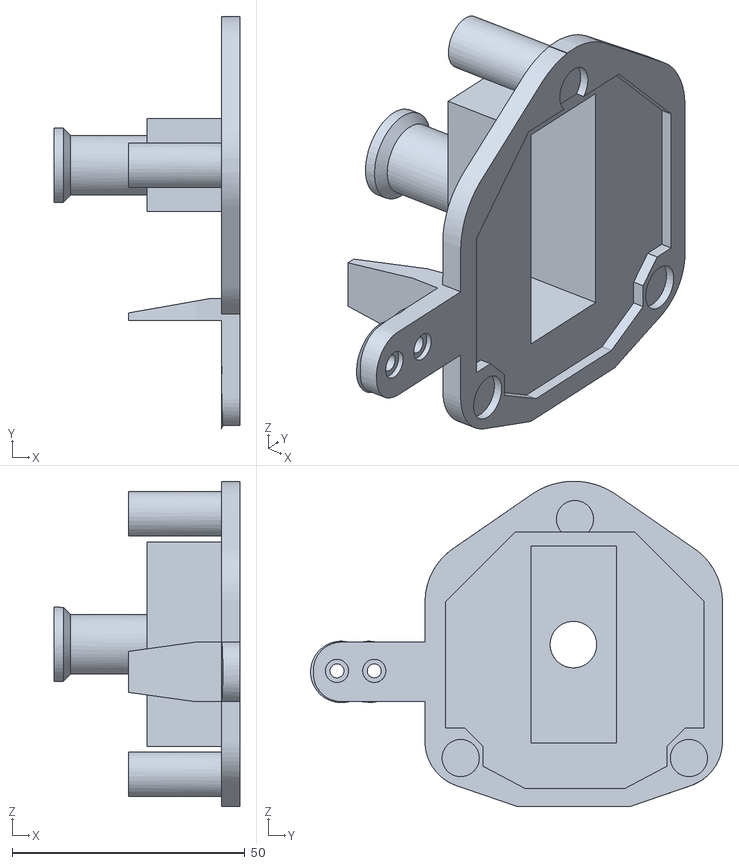
[picture p83: CAD file, 2021-10-04]
stl/Arm/Instruments/InstrumentsCamera.stl
39.9 x 88.5 x 69.9
