JeanetteMueller/OpenPerseverance/stl/RockerBogie/CenterRodMountCover.stl

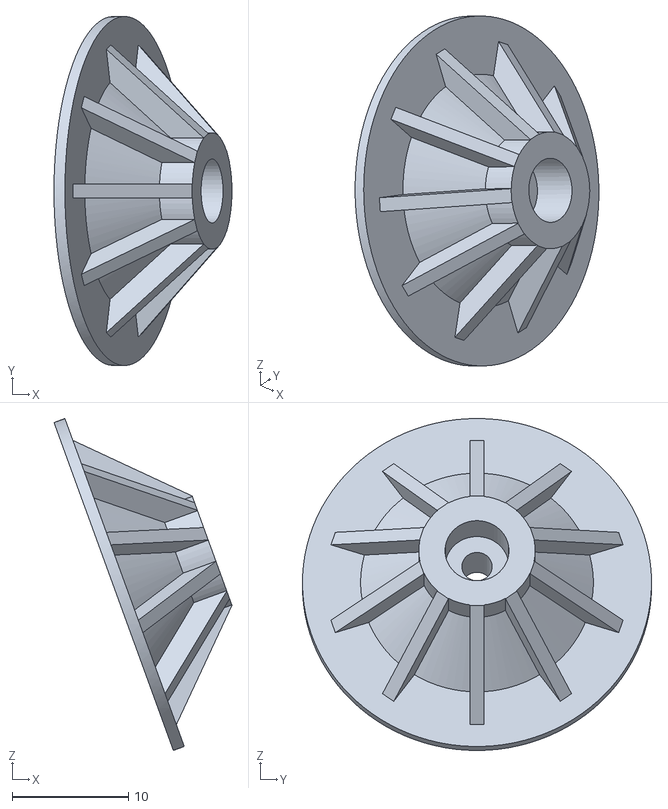
[picture p84: CAD file, 2021-05-24]
stl/RockerBogie/CenterRodMountCover.stl
15.3 x 30.0 x 28.5
