JeanetteMueller/OpenPerseverance/stl/Arm/Instruments/InstrumentsDrill.stl

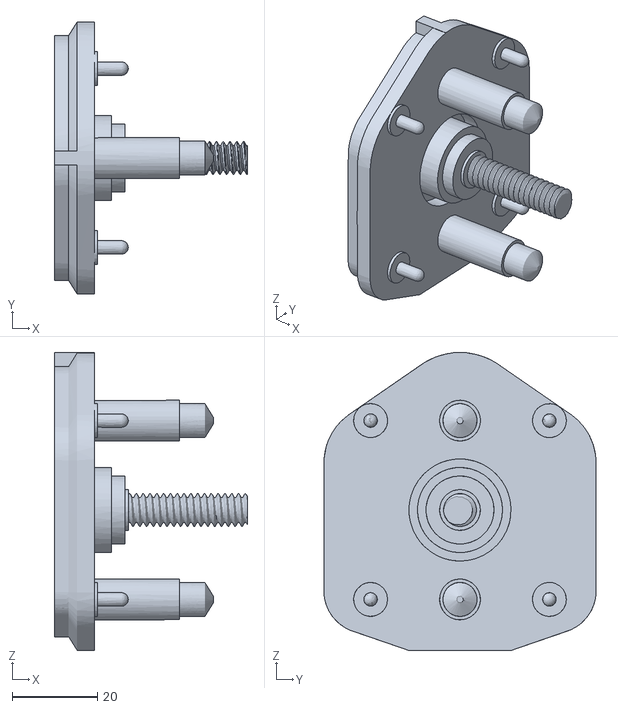
[picture p85: CAD file, 2021-10-04]
stl/Arm/Instruments/InstrumentsDrill.stl
45.3 x 63.9 x 69.9
