JeanetteMueller/OpenPerseverance/stl/HeatExchanger_Left/Heatpipes/HeatExchanger Holder 6.stl

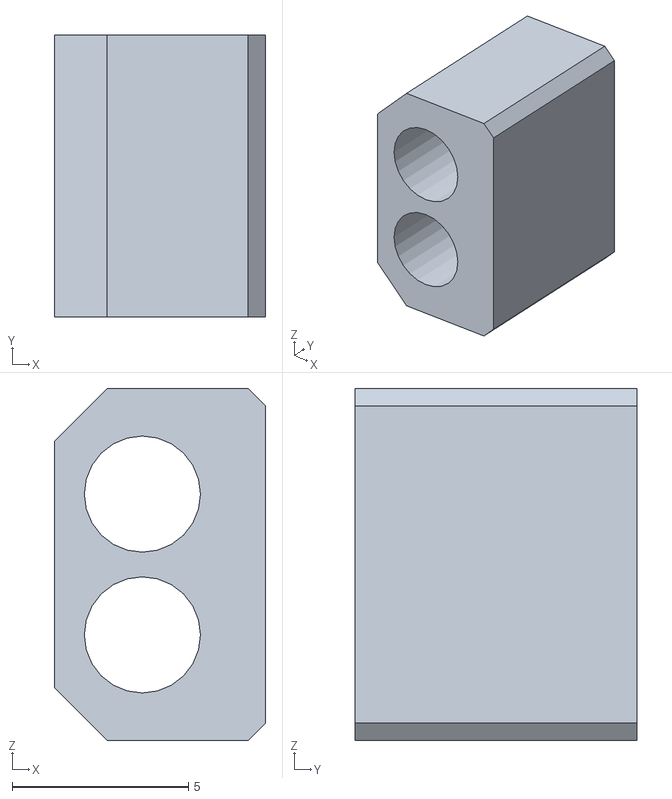
[picture p86: CAD file, 2021-09-22]
stl/HeatExchanger_Left/Heatpipes/HeatExchanger Holder 6.stl
6.00 x 8.00 x 10.0
