JeanetteMueller/OpenPerseverance/stl/RockerBogie/Wheel Rim.stl

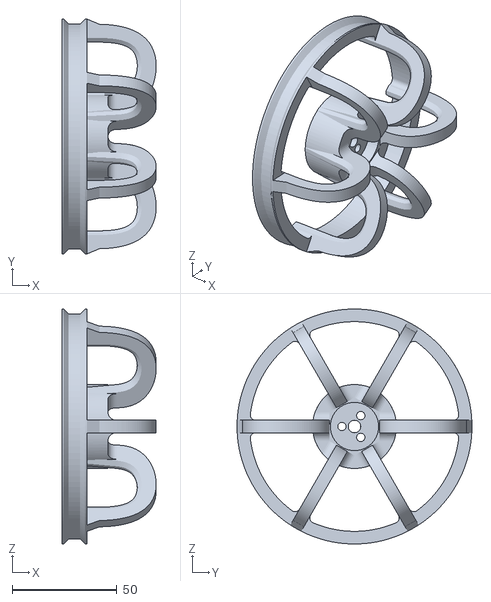
[picture p87: CAD file, 2021-04-15]
stl/RockerBogie/Wheel Rim.stl
45.0 x 112.1 x 112.1
