JeanetteMueller/OpenPerseverance/stl/Arm/Instruments/InstrumentsSherlocWatsonSensor1.stl

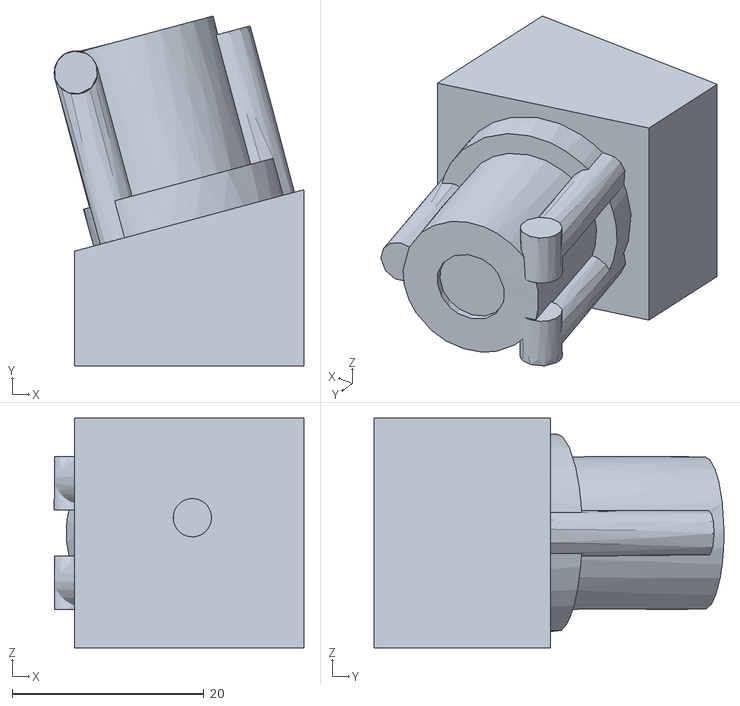
[picture p88: CAD file, 2021-10-04]
stl/Arm/Instruments/InstrumentsSherlocWatsonSensor1.stl
26.1 x 36.5 x 24.0
