JeanetteMueller/OpenPerseverance/stl/RockerBogie/WheelHolder.stl

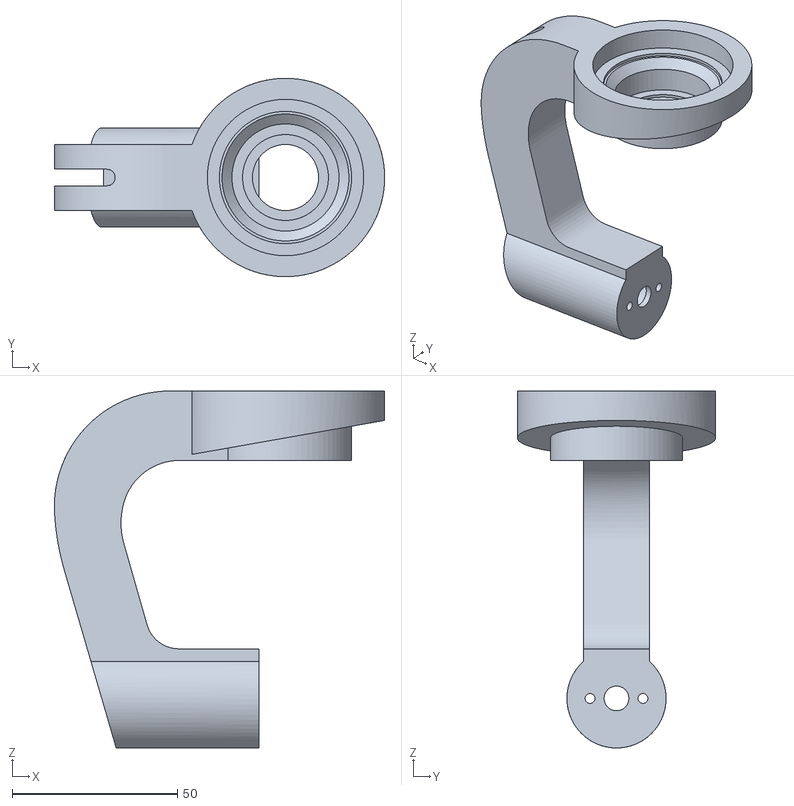
[picture p89: CAD file, 2021-04-15]
stl/RockerBogie/WheelHolder.stl
99.9 x 60.0 x 108.0
