JeanetteMueller/OpenPerseverance/stl/RockerBogie/WheelHolderCenter.stl

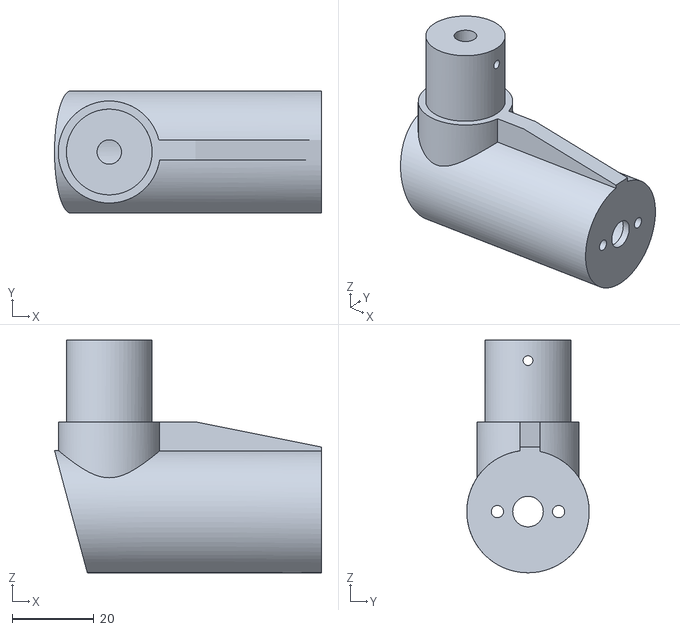
[picture p90: CAD file, 2021-04-15]
stl/RockerBogie/WheelHolderCenter.stl
65.4 x 30.0 x 57.0
