JeanetteMueller/OpenPerseverance/stl/RockerBogie/ServoConnector.stl

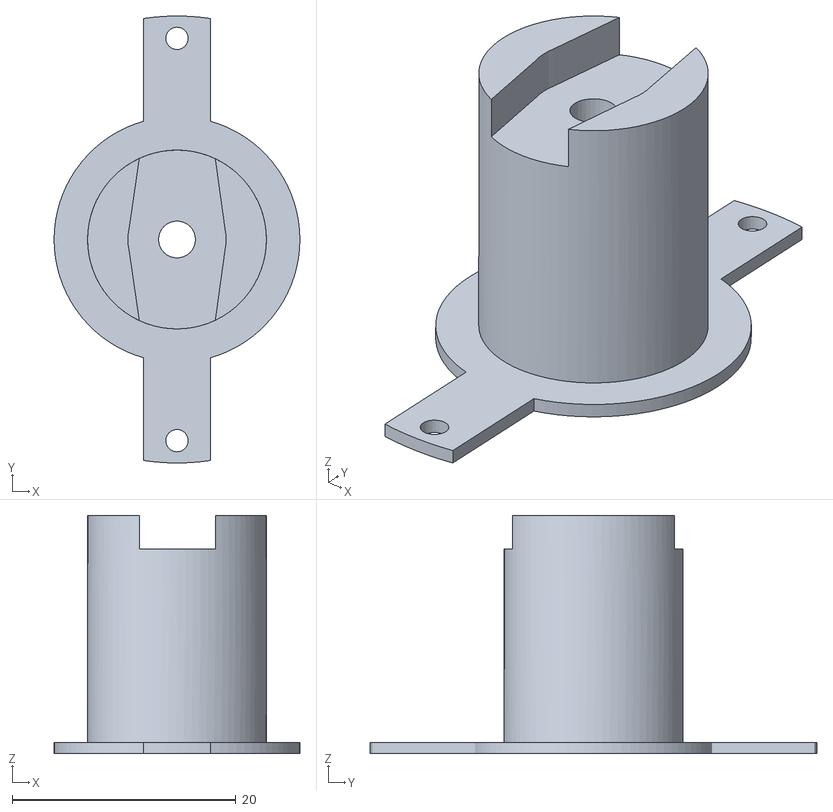
[picture p91: CAD file, 2021-04-12]
stl/RockerBogie/ServoConnector.stl
22.0 x 40.0 x 21.3
