JeanetteMueller/OpenPerseverance/stl/RockerBogie/DifferentialArmHead.stl

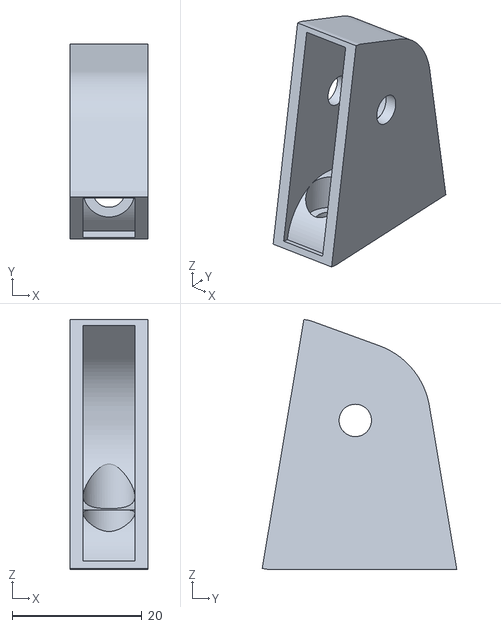
[picture p92: CAD file, 2021-04-12]
stl/RockerBogie/DifferentialArmHead.stl
12.0 x 30.0 x 38.6
