JeanetteMueller/OpenPerseverance/stl/RockerBogie/DifferentialArm.stl

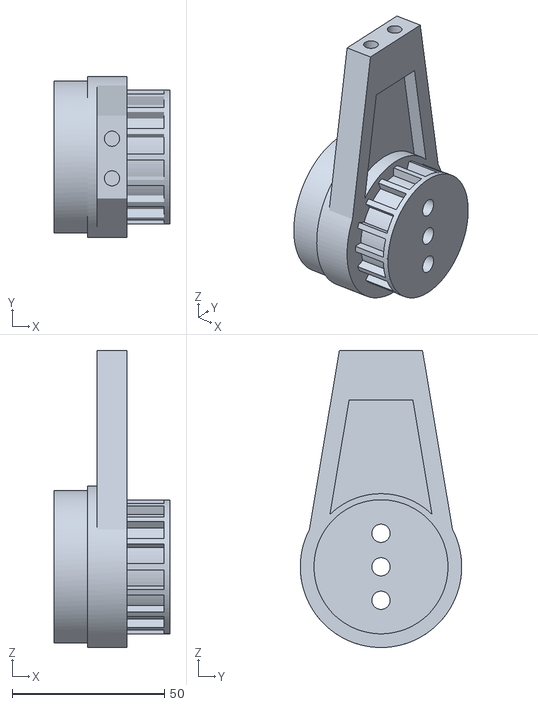
[picture p93: CAD file, 2021-04-12]
stl/RockerBogie/DifferentialArm.stl
38.0 x 53.0 x 97.5
