JeanetteMueller/OpenPerseverance/stl/RockerBogie/RodConnectorFront.stl

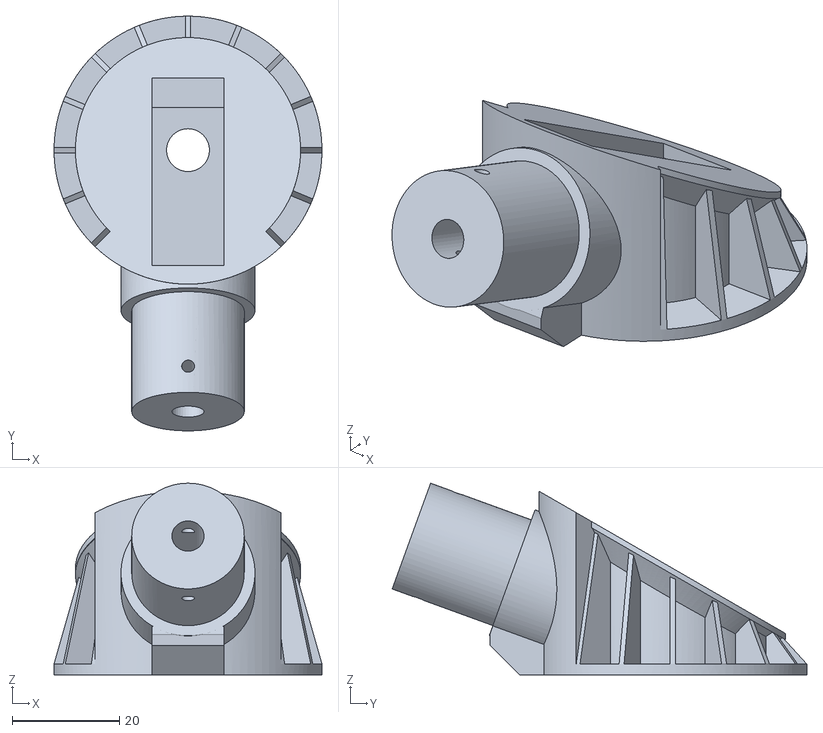
[picture p94: CAD file, 2021-04-12]
stl/RockerBogie/RodConnectorFront.stl
50.0 x 77.4 x 35.8
