JeanetteMueller/OpenPerseverance/stl/RockerBogie/RodConnectorBack.stl

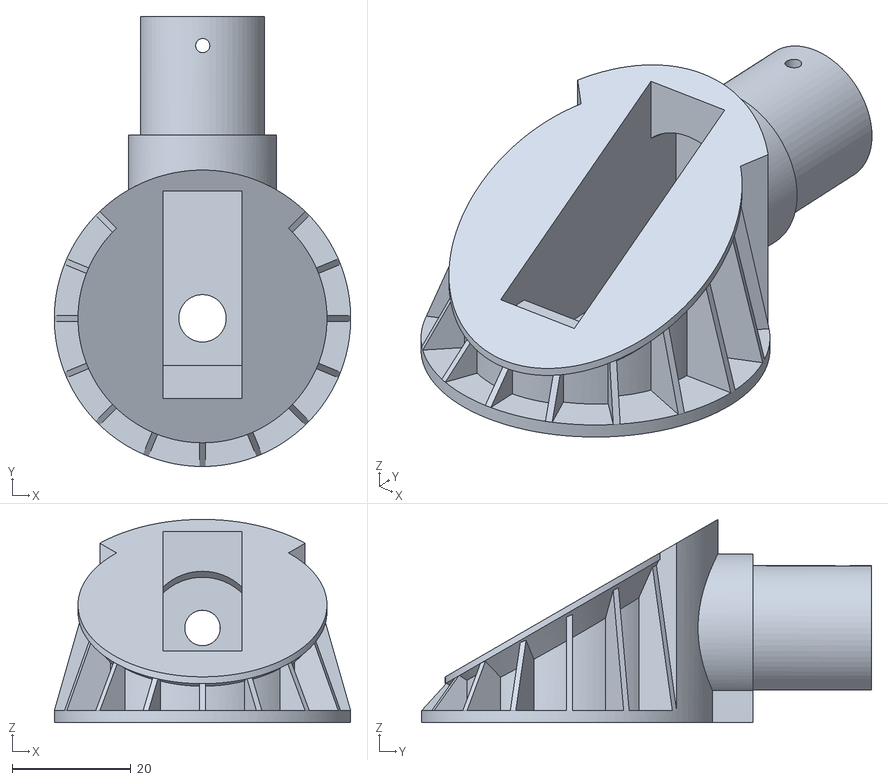
[picture p95: CAD file, 2021-04-12]
stl/RockerBogie/RodConnectorBack.stl
50.0 x 75.9 x 34.3
