JeanetteMueller/OpenPerseverance/stl/RockerBogie/BoogieCenterInternal.stl

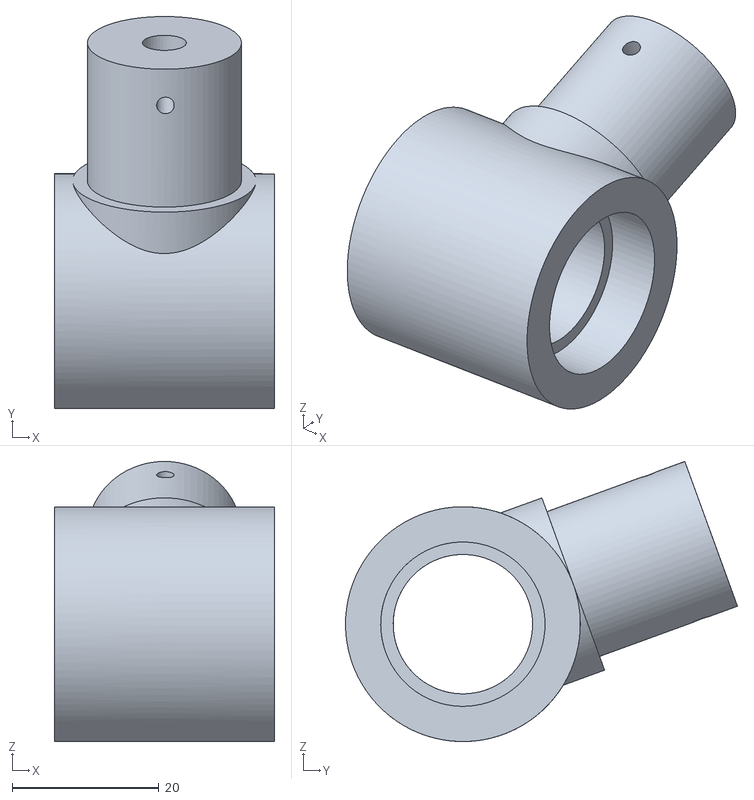
[picture p96: CAD file, 2021-04-12]
stl/RockerBogie/BoogieCenterInternal.stl
30.0 x 53.4 x 38.2
