JeanetteMueller/OpenPerseverance/stl/RockerBogie/BearingCenter.stl

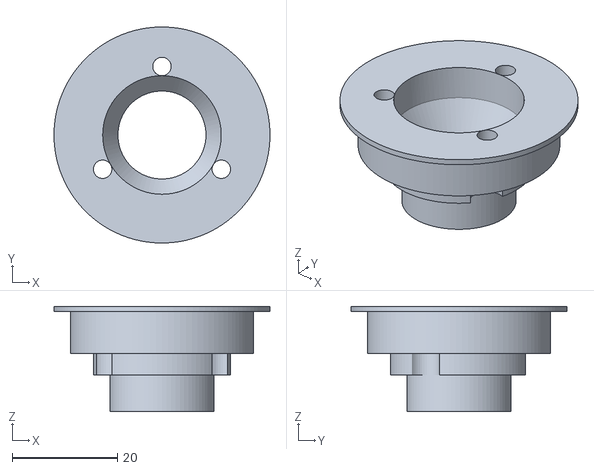
[picture p97: CAD file, 2021-04-12]
stl/RockerBogie/BearingCenter.stl
41.0 x 41.0 x 20.0
