JeanetteMueller/OpenPerseverance/stl/RockerBogie/BalanceArmConnector.stl

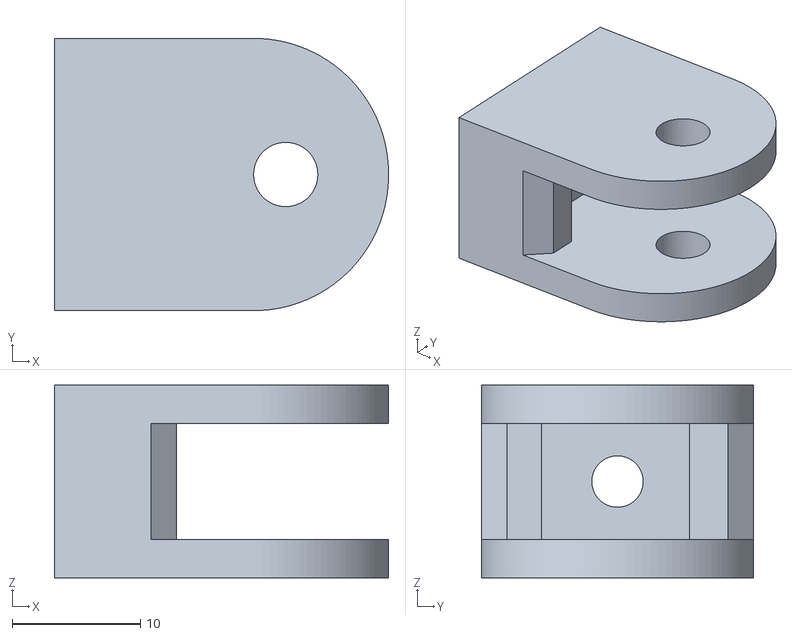
[picture p98: CAD file, 2021-04-12]
stl/RockerBogie/BalanceArmConnector.stl
26.0 x 21.2 x 15.0
